t-dsp/t-dsp_desktop_pro/3d_models/so-14-soic14-1.snapshot.2/Renderings/soic-14.JPG

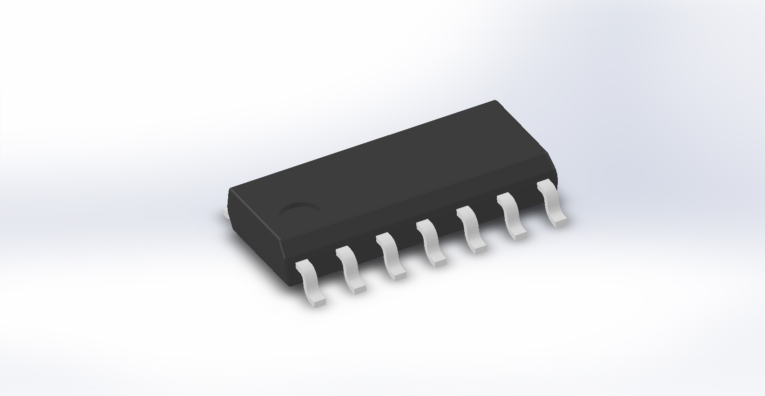
3d_models/so-14-soic14-1.snapshot.2/Renderings/soic-14.JPG
