t-dsp/t-dsp_desktop_pro/3d_models/teensy-4-0-1.snapshot.3/Teensy_4.0/Teensy_4.0_Decal/ARM_Coretex M7 Chip Decal.png

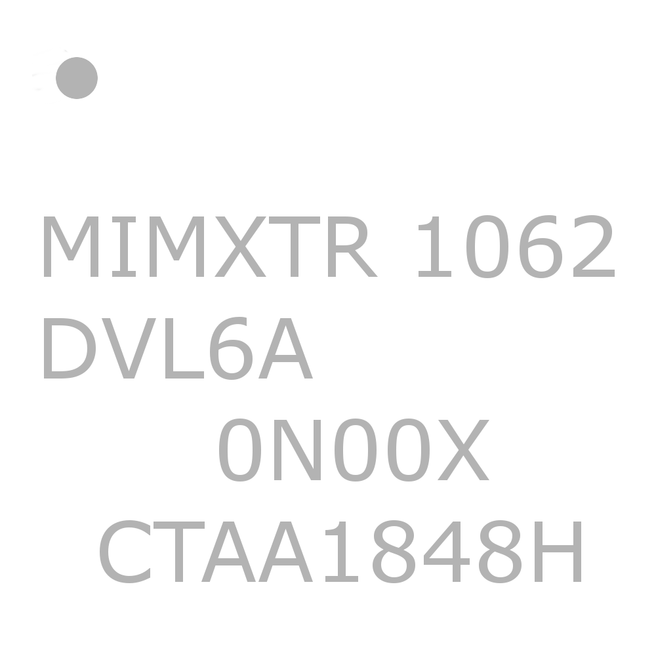
3d_models/teensy-4-0-1.snapshot.3/Teensy_4.0/Teensy_4.0_Decal/ARM_Coretex M7 Chip Decal.png
