t-dsp/t-dsp_desktop_pro/documentation/t-dsp-desktop-pro-3d-angle_back.png

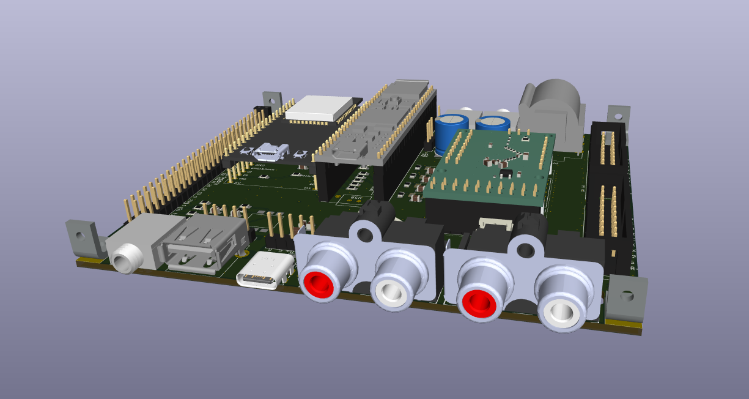
documentation/t-dsp-desktop-pro-3d-angle_back.png
