t-dsp/t-dsp_desktop_pro/documentation/t-dsp-desktop-pro-3d-bottom.png

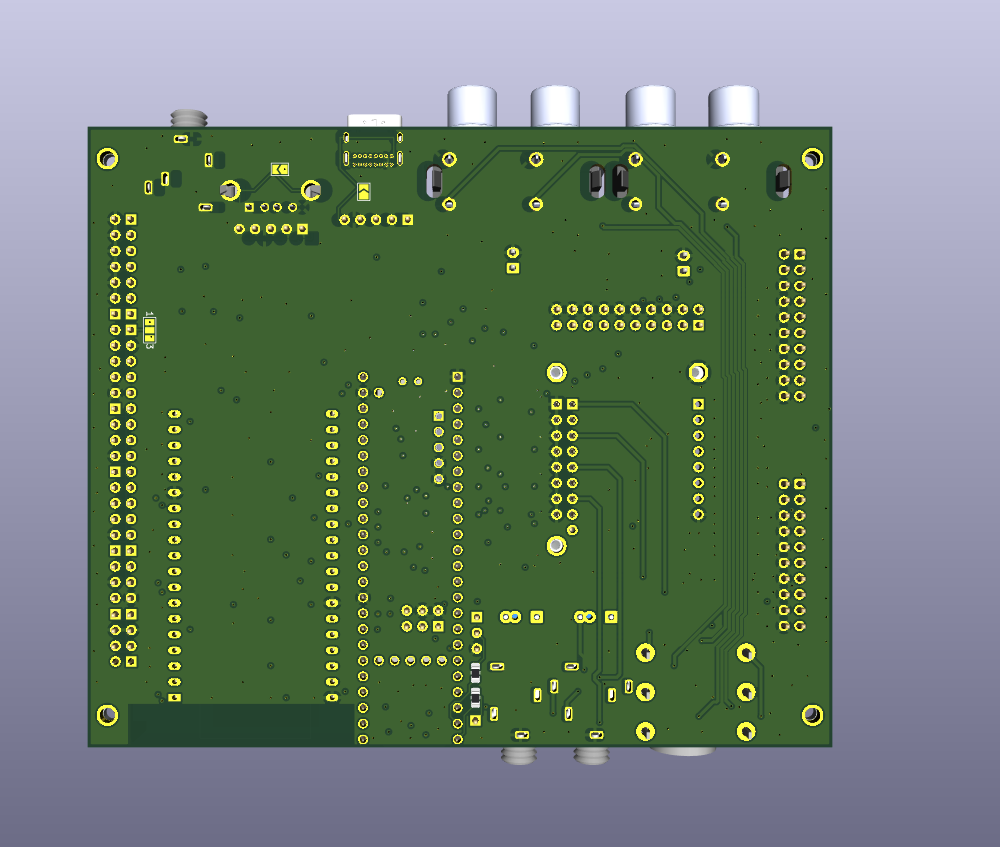
documentation/t-dsp-desktop-pro-3d-bottom.png
