t-dsp/t-dsp_desktop_pro/documentation/t-dsp-desktop-pro-pcb-layout.png

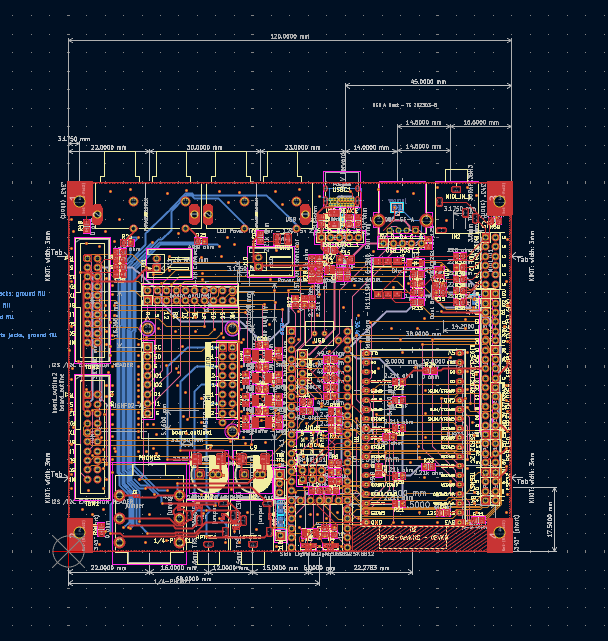
documentation/t-dsp-desktop-pro-pcb-layout.png
