t-dsp/t-dsp_desktop_pro/3d_models/raspberry-pi-4-model-b-1.snapshot.3/Microphone Plug, RPi4ModelB.SLDPRT

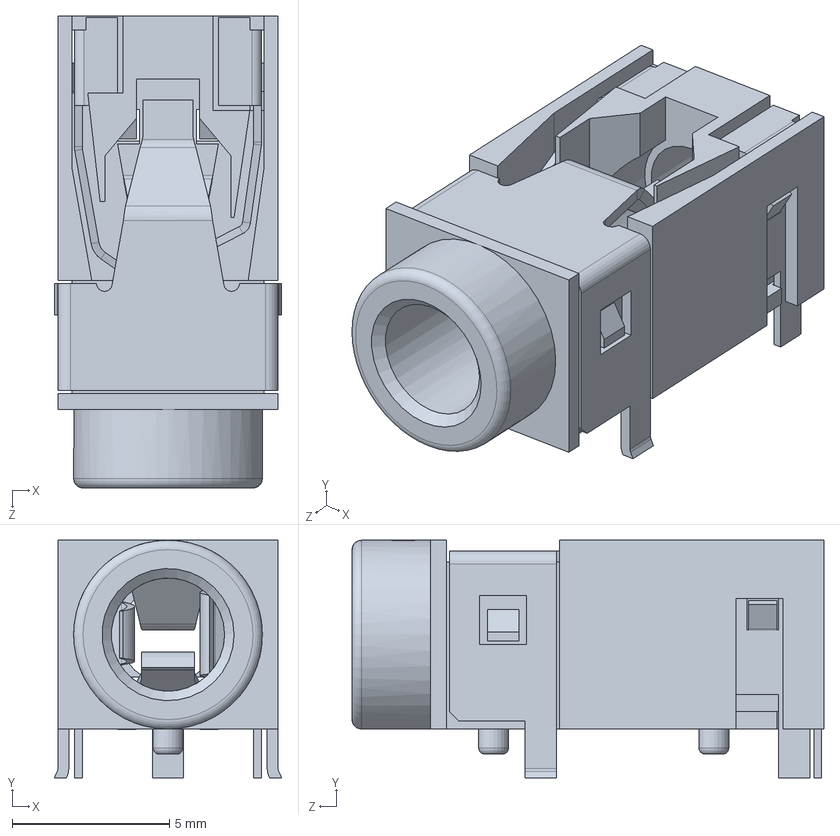
[picture p26: CAD file, 2025-03-24]
3d_models/raspberry-pi-4-model-b-1.snapshot.3/Microphone Plug, RPi4ModelB.SLDPRT
7.23 x 7.55 x 15.0 mm
