t-dsp/t-dsp_desktop_pro/3d_models/raspberry-pi-4-model-b-1.snapshot.3/2.54 mm DUPONT MALE PIN HEADER, POE, 2X2, RPi4ModelB.SLDPRT

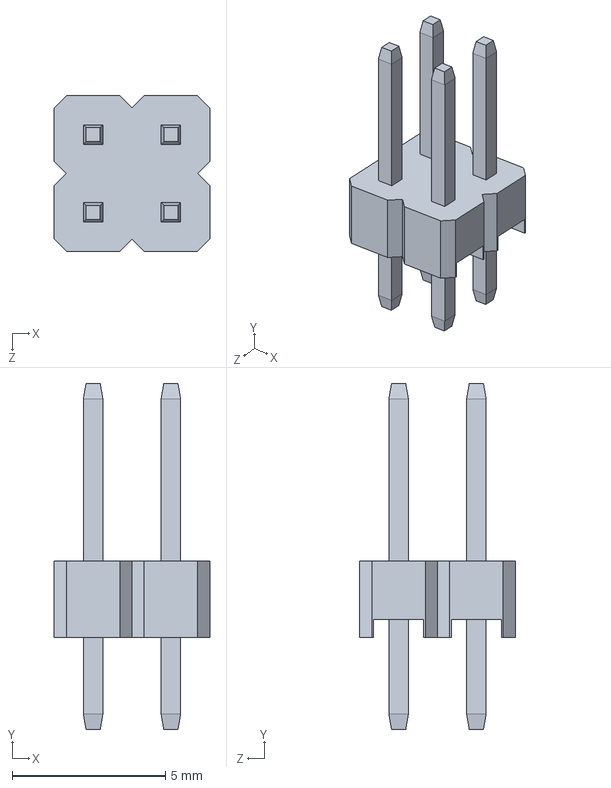
[picture p30: CAD file, 2025-03-24]
3d_models/raspberry-pi-4-model-b-1.snapshot.3/2.54 mm DUPONT MALE PIN HEADER, POE, 2X2, RPi4ModelB.SLDPRT
5.08 x 11.3 x 5.08 mm
