t-dsp/t-dsp_desktop_pro/lib_fp/project_fp/TYPE-C-31-M-12.step

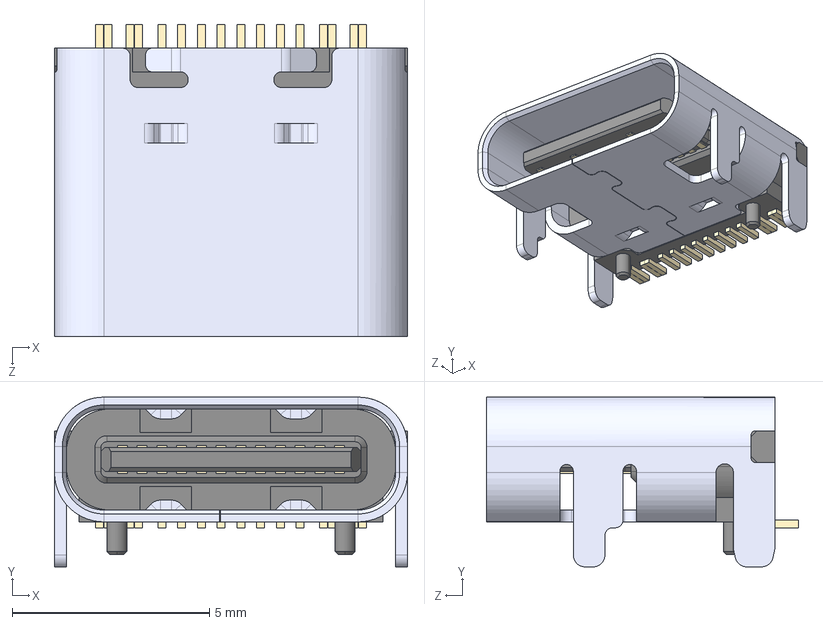
[picture p32: CAD file, 2025-03-24]
lib_fp/project_fp/TYPE-C-31-M-12.step
8.94 x 4.30 x 7.90 mm
