t-dsp/t-dsp_desktop_pro/3d_models/audio_project_board_step/teensy41_audio_project_board_end1.step

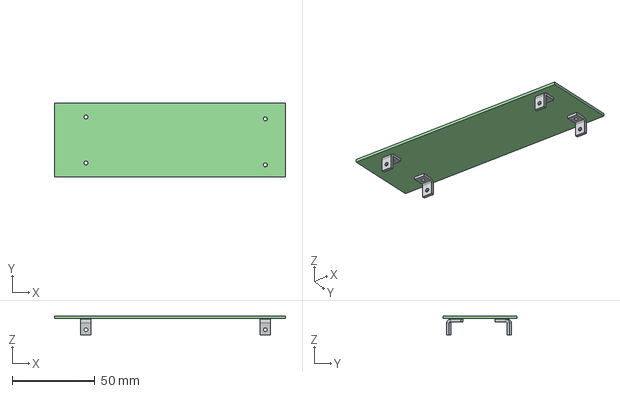
[picture p33: CAD file, 2025-03-24]
3d_models/audio_project_board_step/teensy41_audio_project_board_end1.step
139.7 x 44.5 x 11.5 mm
front_panel PCB
