t-dsp/t-dsp_desktop_pro/3d_models/raspberry-pi-4-model-b-1.snapshot.3/2X USB3.0 PORTS, RPi4ModelB.SLDPRT

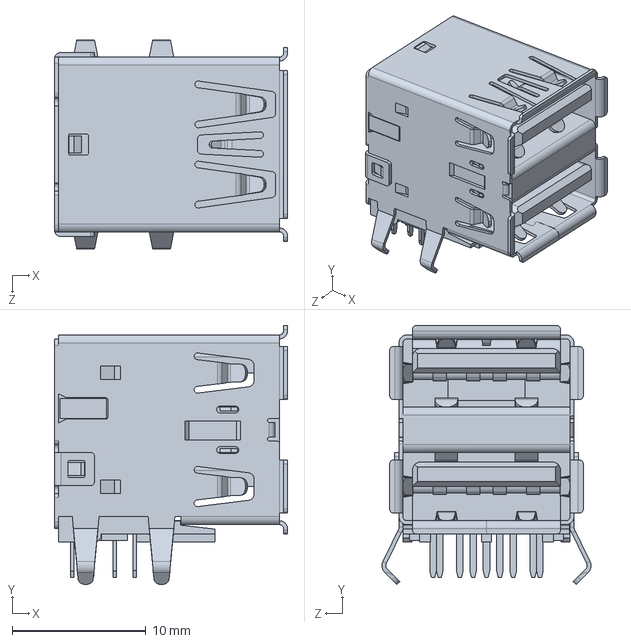
[picture p34: CAD file, 2025-03-24]
3d_models/raspberry-pi-4-model-b-1.snapshot.3/2X USB3.0 PORTS, RPi4ModelB.SLDPRT
17.5 x 19.4 x 15.7 mm
