t-dsp/t-dsp_desktop_pro/3d_models/teensy-4-0-1.snapshot.3/Teensy_4.0/SKRPACE010 v4.SLDPRT

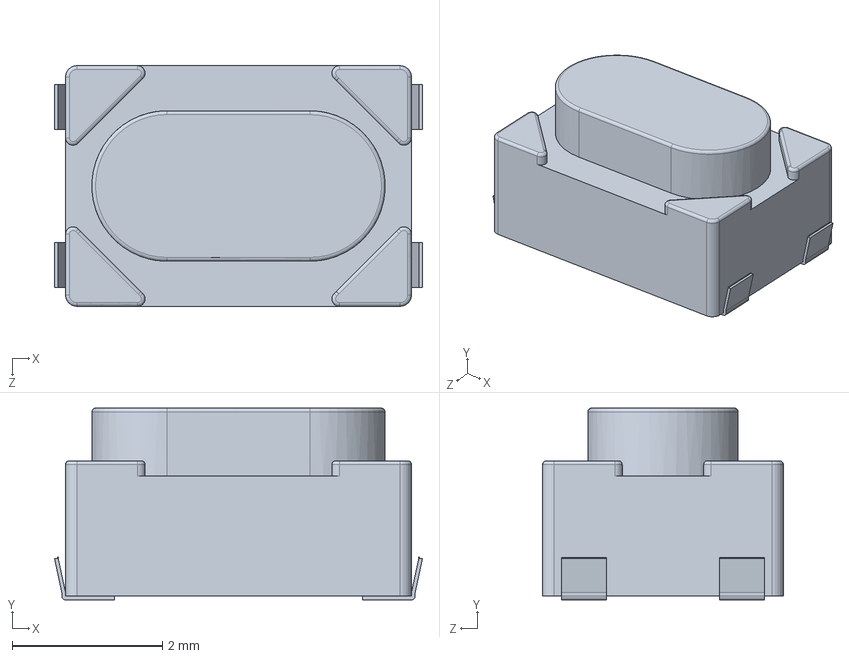
[picture p35: CAD file, 2025-03-24]
3d_models/teensy-4-0-1.snapshot.3/Teensy_4.0/SKRPACE010 v4.SLDPRT
4.89 x 2.55 x 3.20 mm
