t-dsp/t-dsp_desktop_pro/3d_models/TPD4E02B04DQA.step

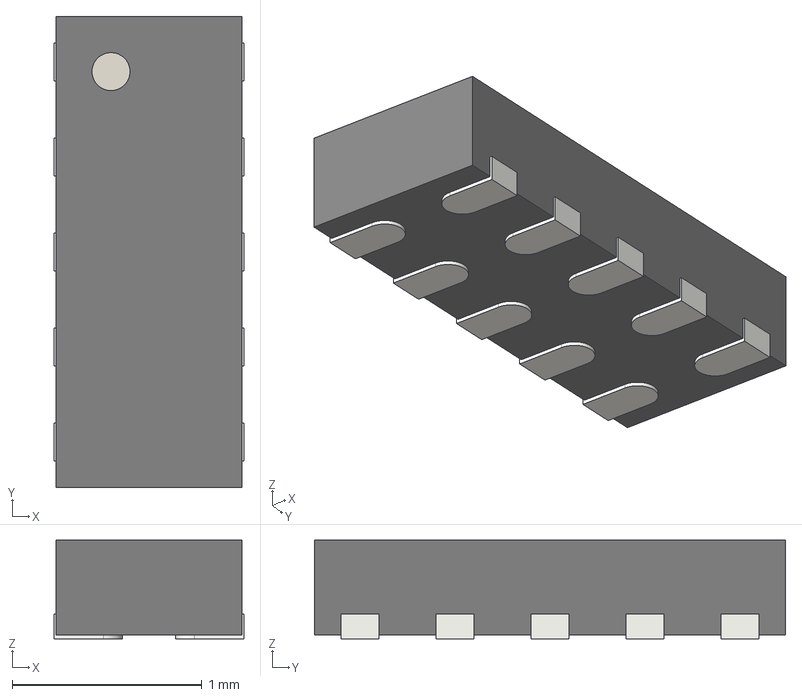
[picture p36: CAD file, 2026-02-23]
3d_models/TPD4E02B04DQA.step
1.00 x 2.48 x 0.52 mm
