t-dsp/t-dsp_desktop_pro/3d_models/audio_project_board_step/teensy41_audio_project_board_fp_c_back.step

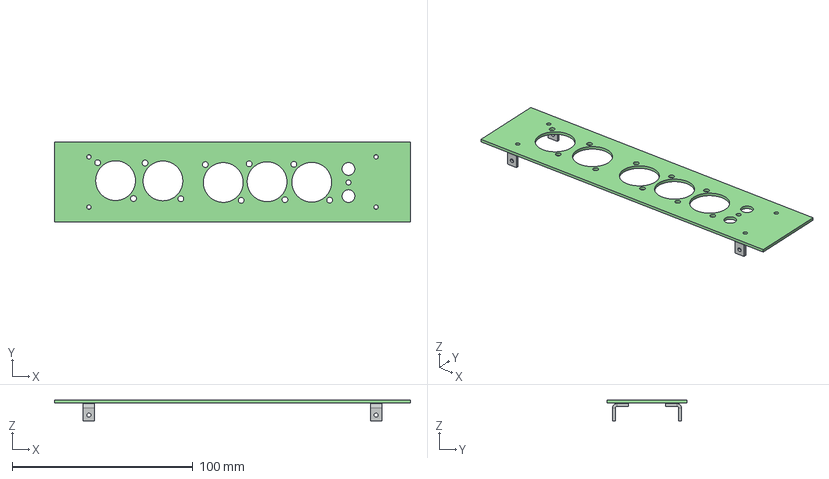
[picture p37: CAD file, 2025-03-24]
3d_models/audio_project_board_step/teensy41_audio_project_board_fp_c_back.step
196.8 x 44.5 x 11.5 mm
front_panel PCB
