t-dsp/t-dsp_desktop_pro/3d_models/raspberry-pi-4-model-b-1.snapshot.3/Broadcom BCM54213PE Gigabit Ethernet Transceiver, RPi4ModelB.SLDPRT

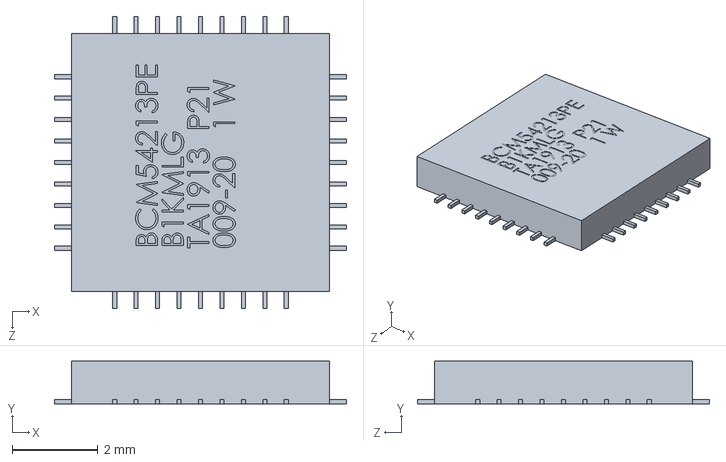
[picture p38: CAD file, 2025-03-24]
3d_models/raspberry-pi-4-model-b-1.snapshot.3/Broadcom BCM54213PE Gigabit Ethernet Transceiver, RPi4ModelB.SLDPRT
6.80 x 1.00 x 6.80 mm
