t-dsp/t-dsp_desktop_pro/3d_models/TPS2116DRLR.stp

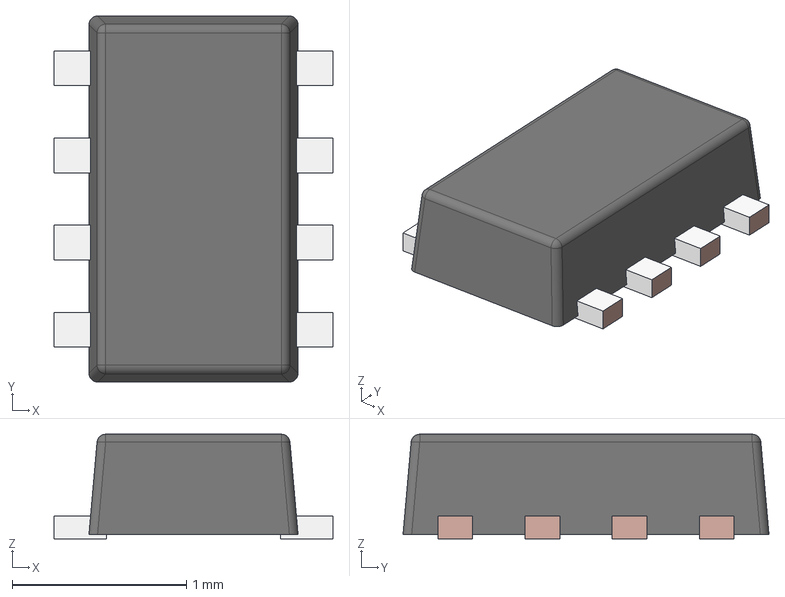
[picture p39: CAD file, 2026-02-23]
3d_models/TPS2116DRLR.stp
1.60 x 2.10 x 0.6 mm
FRAME-DRL0008A
BODY-SOT
