t-dsp/t-dsp_desktop_pro/lib_fp/project_fp/USB4085-GF-A_REVA4.step

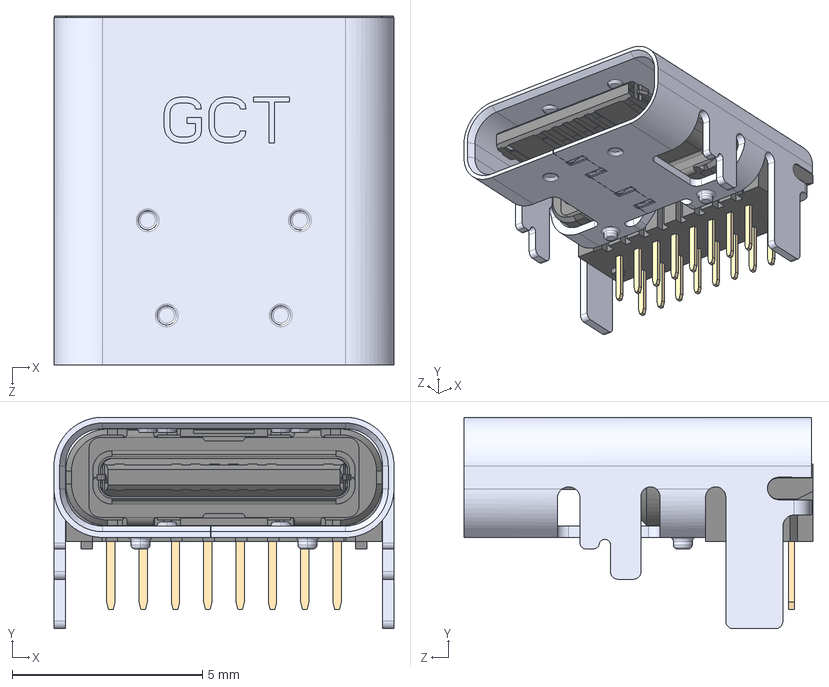
[picture p40: CAD file, 2025-03-24]
lib_fp/project_fp/USB4085-GF-A_REVA4.step
8.94 x 5.56 x 9.17 mm
USB4085-GF-A_PART2
USB4085-GF-A_PART1_1
Part27^USB4085-GF-A_1
