t-dsp/t-dsp_desktop_pro/3d_models/audio_project_board_step/teensy41_audio_project_board_lid.step

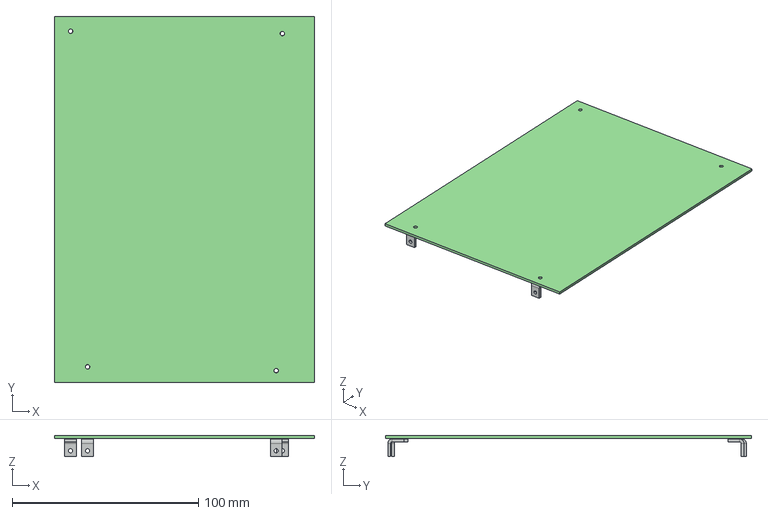
[picture p41: CAD file, 2025-03-24]
3d_models/audio_project_board_step/teensy41_audio_project_board_lid.step
139.7 x 196.8 x 11.5 mm
_autosave-front_panel PCB
