t-dsp/t-dsp_desktop_pro/3d_models/raspberry-pi-4-model-b-1.snapshot.3/VIA VL805 PCIe USB 3.0 controller, RPi4ModelB.SLDPRT

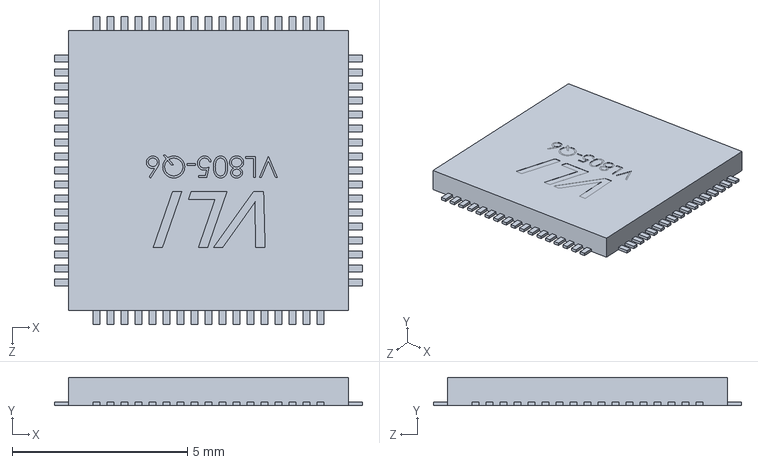
[picture p42: CAD file, 2025-03-24]
3d_models/raspberry-pi-4-model-b-1.snapshot.3/VIA VL805 PCIe USB 3.0 controller, RPi4ModelB.SLDPRT
8.80 x 0.8 x 8.80 mm
