t-dsp/t-dsp_desktop_pro/3d_models/teensy-4-0-1.snapshot.3/Teensy_4.0/Micro USB-B Female 5Pin SMD.SLDPRT

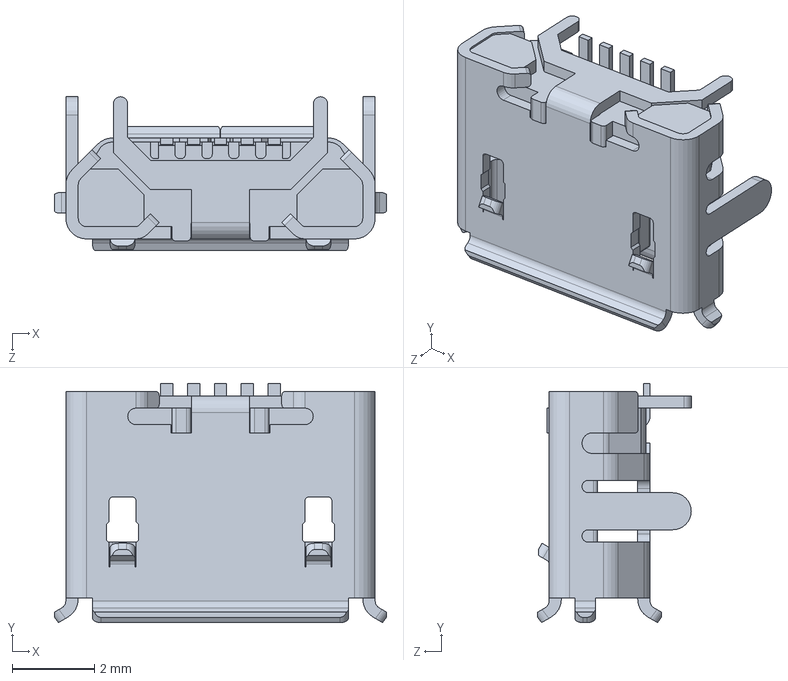
[picture p43: CAD file, 2025-03-24]
3d_models/teensy-4-0-1.snapshot.3/Teensy_4.0/Micro USB-B Female 5Pin SMD.SLDPRT
8.05 x 5.80 x 3.72 mm
