t-dsp/t-dsp_desktop_pro/3d_models/raspberry-pi-4-model-b-1.snapshot.3/2X USB2.0 PORTS, RPi4ModelB.SLDPRT

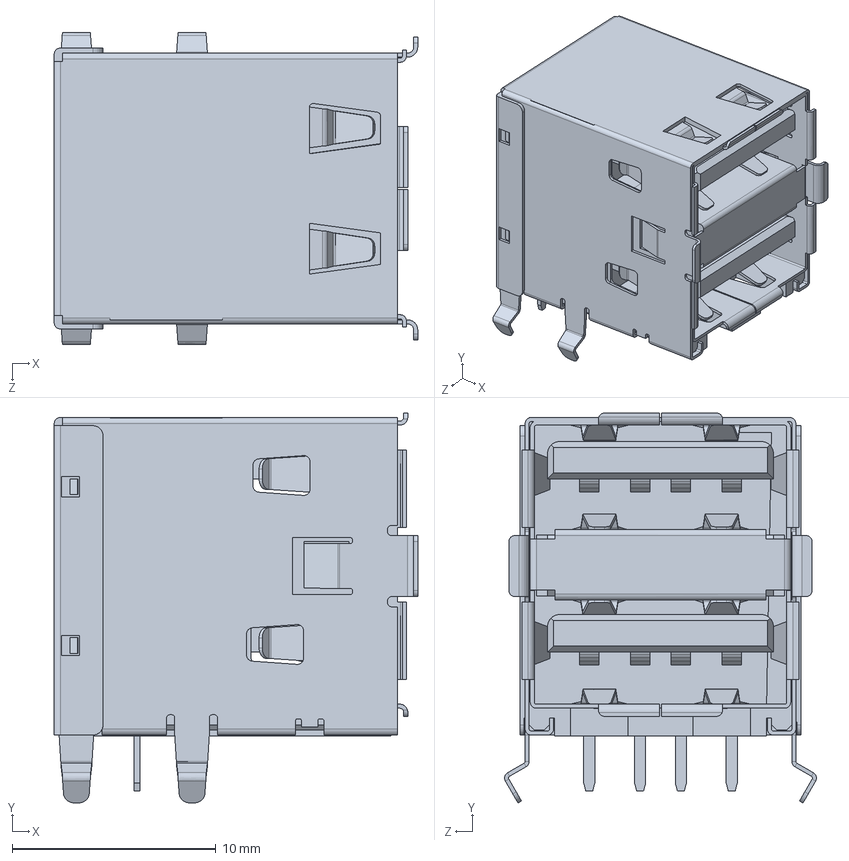
[picture p44: CAD file, 2025-03-24]
3d_models/raspberry-pi-4-model-b-1.snapshot.3/2X USB2.0 PORTS, RPi4ModelB.SLDPRT
17.9 x 19.2 x 15.3 mm
