t-dsp/t-dsp_desktop_pro/3d_models/TPD1E10B06DPYT.stp

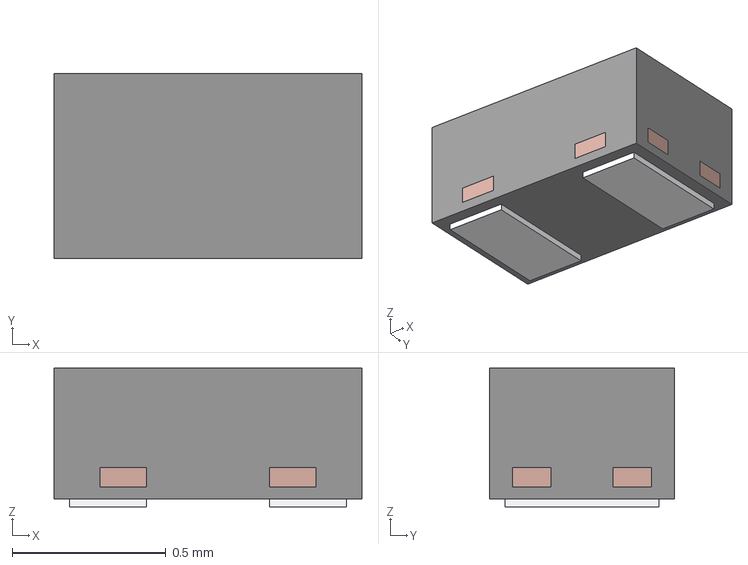
[picture p45: CAD file, 2026-02-23]
3d_models/TPD1E10B06DPYT.stp
1.00 x 0.6 x 0.45 mm
BODY-SON
FRAME-DPY0002A
