t-dsp/t-dsp_desktop_pro/3d_models/JST_EH_S2B-EH_1x02_P2.50mm_Horizontal.step

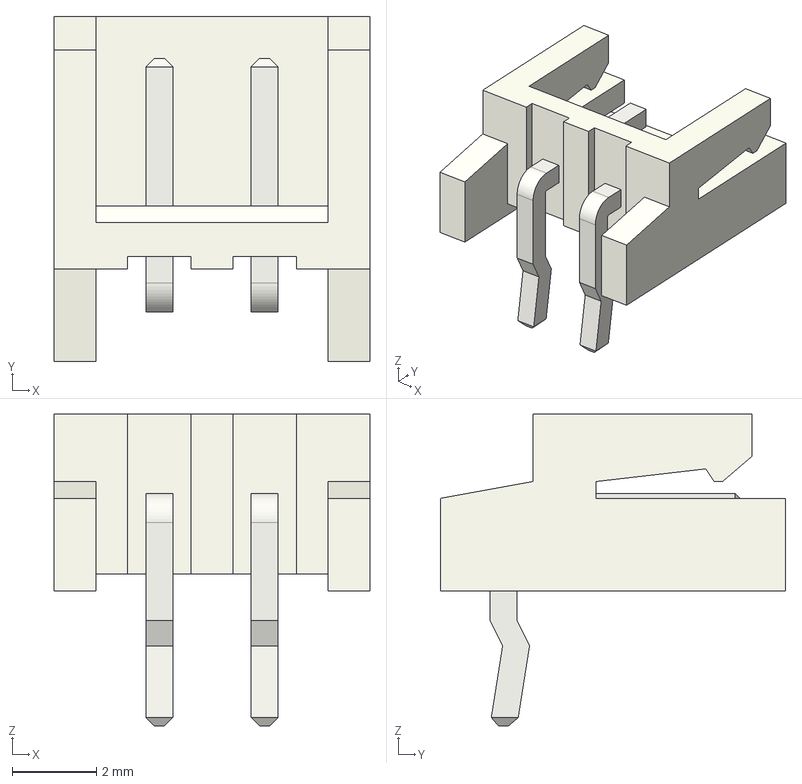
[picture p46: CAD file, 2026-02-20]
3d_models/JST_EH_S2B-EH_1x02_P2.50mm_Horizontal.step
7.50 x 8.20 x 7.40 mm
