t-dsp/t-dsp_desktop_pro/3d_models/raspberry-pi-4-model-b-1.snapshot.3/Female Micro HDMI Connector, RPi4ModelB.SLDPRT

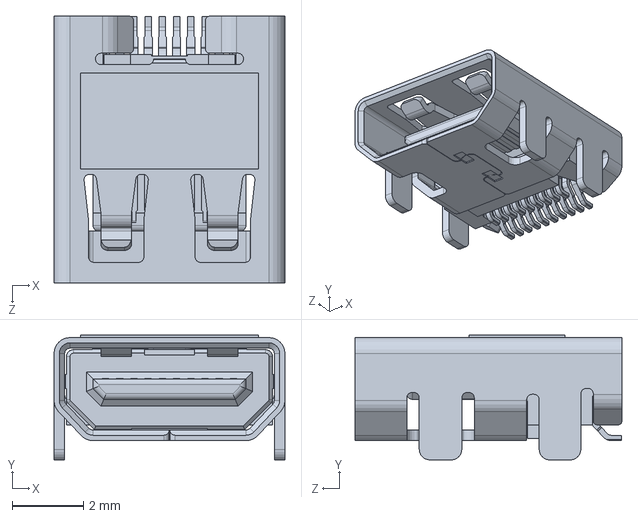
[picture p47: CAD file, 2025-03-24]
3d_models/raspberry-pi-4-model-b-1.snapshot.3/Female Micro HDMI Connector, RPi4ModelB.SLDPRT
6.50 x 3.52 x 7.50 mm
