t-dsp/t-dsp_desktop_pro/3d_models/PinSocket_1x01_P2.54mm_Vertical.step

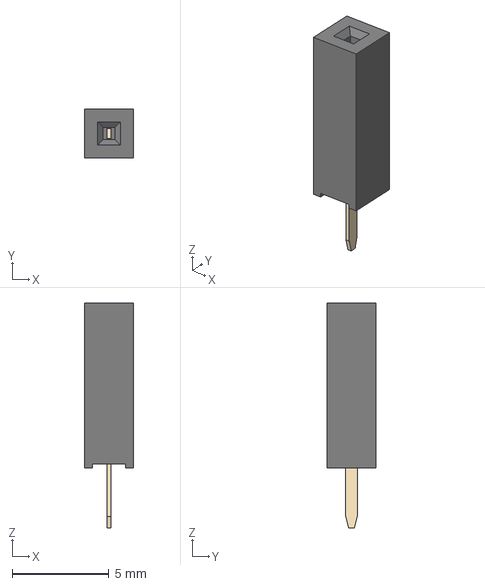
[picture p48: CAD file, 2026-02-20]
3d_models/PinSocket_1x01_P2.54mm_Vertical.step
2.54 x 2.54 x 11.6 mm
