t-dsp/t-dsp_desktop_pro/3d_models/raspberry-pi-4-model-b-1.snapshot.3/Female USB Type C Connector, RPi4ModelB.SLDPRT

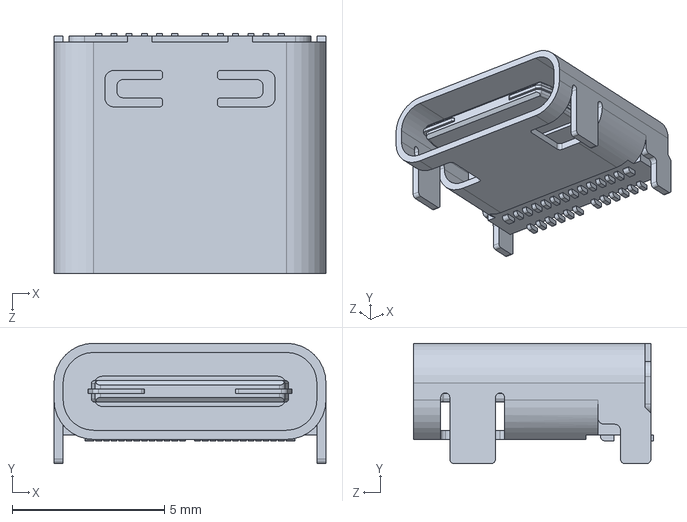
[picture p49: CAD file, 2025-03-24]
3d_models/raspberry-pi-4-model-b-1.snapshot.3/Female USB Type C Connector, RPi4ModelB.SLDPRT
8.94 x 3.96 x 7.90 mm
