t-dsp/t-dsp_desktop_pro/3d_models/H11L1SM.step

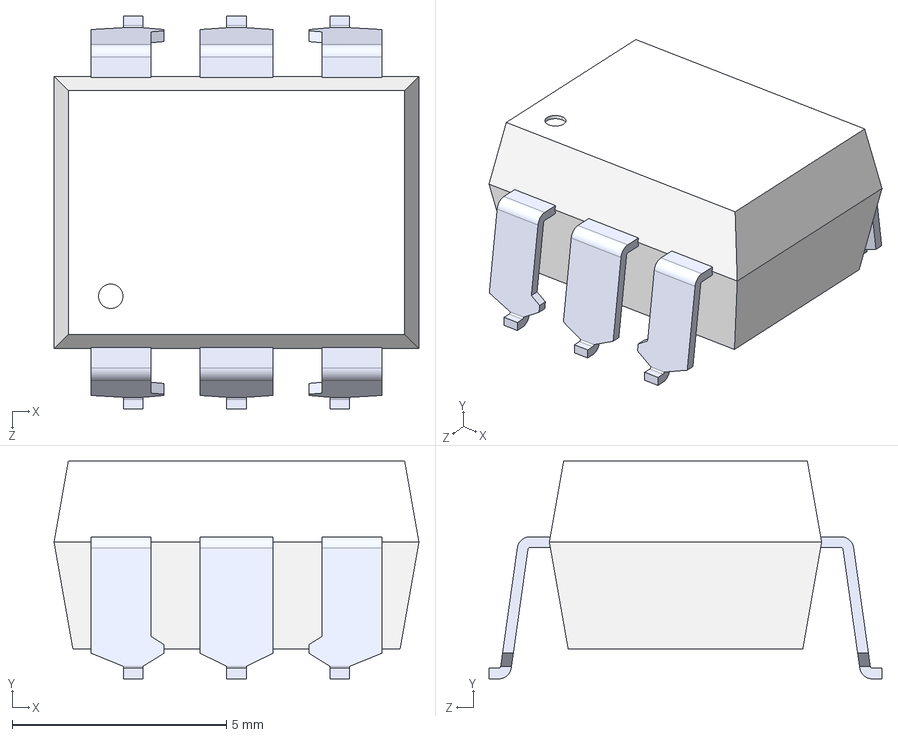
[picture p50: CAD file, 2026-02-20]
3d_models/H11L1SM.step
8.51 x 5.08 x 9.17 mm
