t-dsp/t-dsp_desktop_pro/3d_models/LED_D5.0mm_Clear.step

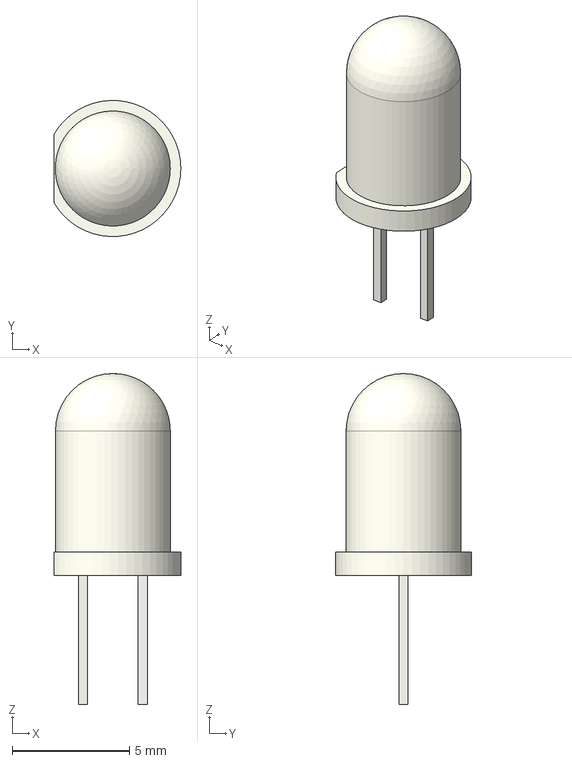
[picture p55: CAD file, 2026-02-20]
3d_models/LED_D5.0mm_Clear.step
5.40 x 5.79 x 14.1 mm
