t-dsp/t-dsp_desktop_pro/3d_models/SOT-23-5.step

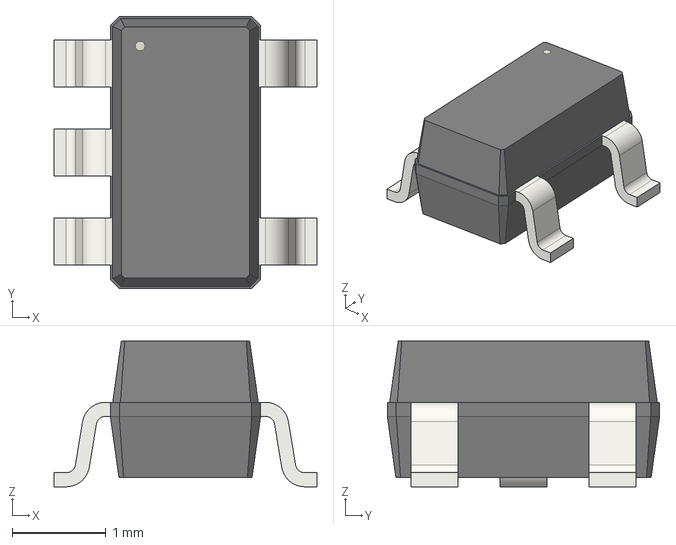
[picture p56: CAD file, 2026-02-20]
3d_models/SOT-23-5.step
2.80 x 2.90 x 1.55 mm
