t-dsp/t-dsp_desktop_pro/3d_models/CP_Radial_D10.0mm_P5.00mm.step

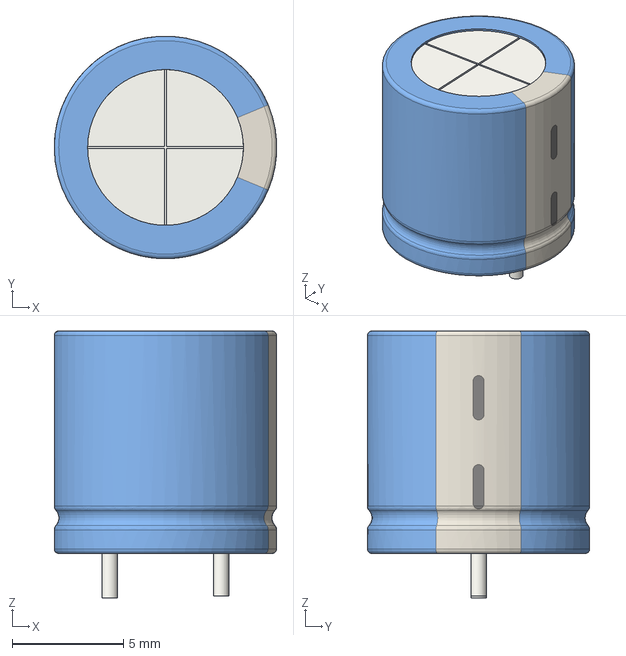
[picture p58: CAD file, 2026-02-11]
3d_models/CP_Radial_D10.0mm_P5.00mm.step
10.00 x 9.99 x 12.0 mm
