t-dsp/t-dsp_desktop_pro/3d_models/D_1210_3225Metric.step

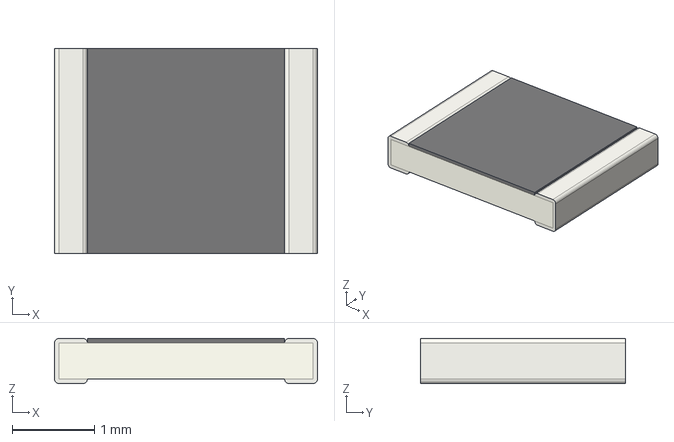
[picture p60: CAD file, 2026-02-11]
3d_models/D_1210_3225Metric.step
3.20 x 2.50 x 0.55 mm
