t-dsp/t-dsp_desktop_pro/3d_models/IDC-Header_2x10_P2.54mm_Vertical.step

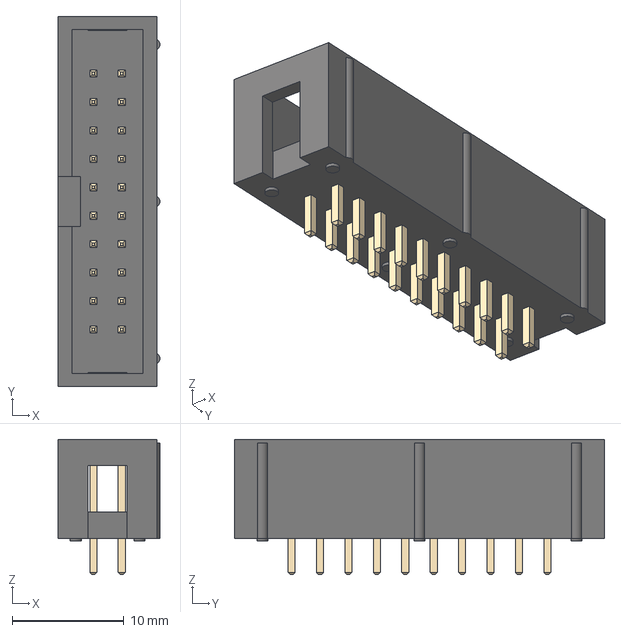
[picture p61: CAD file, 2026-02-11]
3d_models/IDC-Header_2x10_P2.54mm_Vertical.step
9.10 x 33.1 x 12.1 mm
