t-dsp/t-dsp_desktop_pro/3d_models/SOT-583-8.step

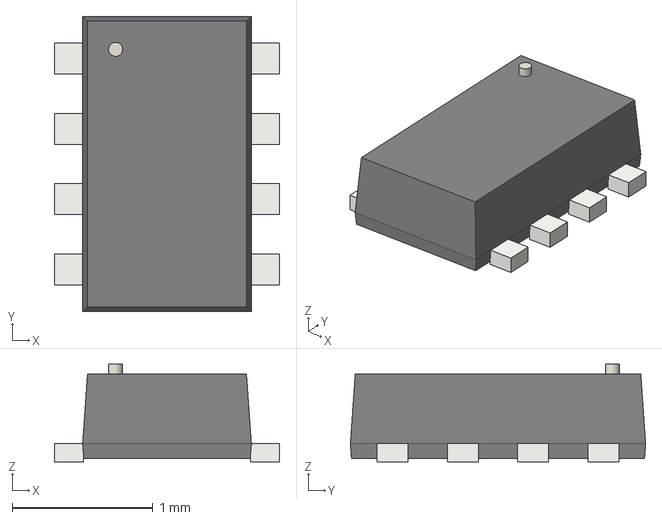
[picture p62: CAD file, 2026-02-11]
3d_models/SOT-583-8.step
1.60 x 2.10 x 0.695 mm
