t-dsp/t-dsp_desktop_pro/3d_models/PinHeader_1x06_P2.54mm_Vertical.step

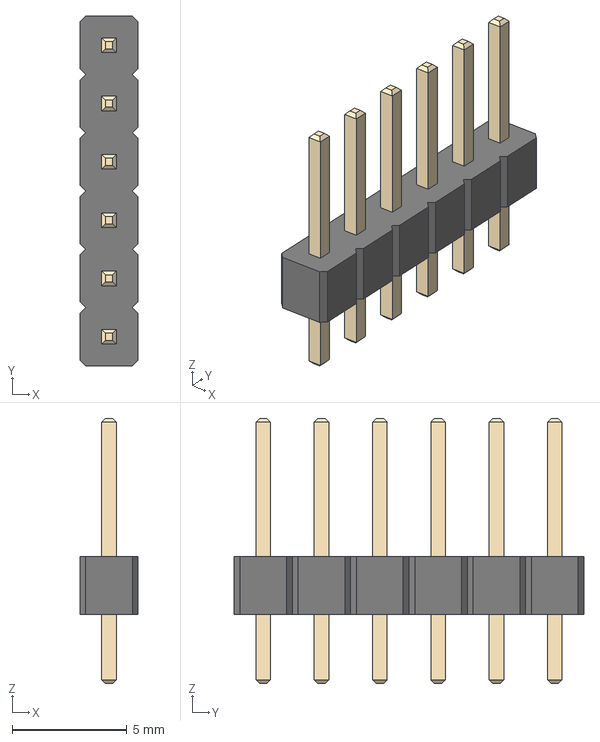
[picture p63: CAD file, 2026-02-11]
3d_models/PinHeader_1x06_P2.54mm_Vertical.step
2.54 x 15.2 x 11.5 mm
