t-dsp/t-dsp_desktop_pro/3d_models/C_1206_3216Metric.step

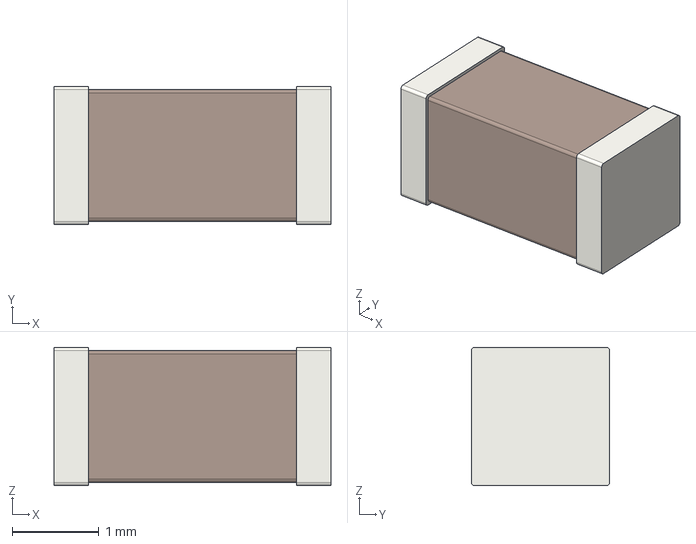
[picture p66: CAD file, 2026-02-11]
3d_models/C_1206_3216Metric.step
3.20 x 1.60 x 1.60 mm
