t-dsp/t-dsp_desktop_pro/3d_models/PinSocket_2x10_P2.54mm_Vertical.step

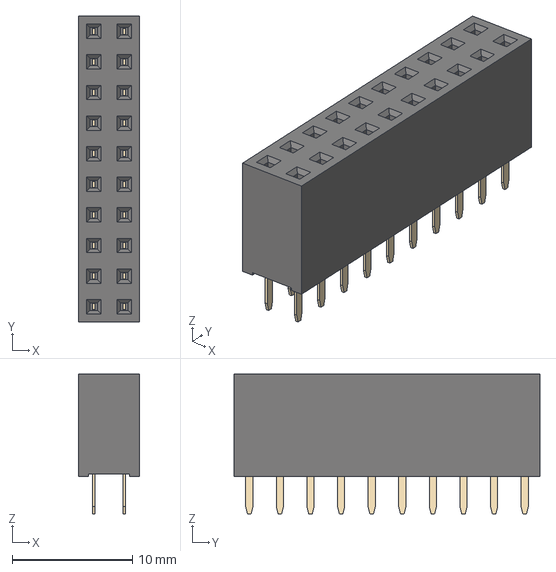
[picture p69: CAD file, 2026-02-11]
3d_models/PinSocket_2x10_P2.54mm_Vertical.step
5.08 x 25.4 x 11.6 mm
