t-dsp/t-dsp_desktop_pro/3d_models/PinSocket_1x02_P2.54mm_Vertical.step

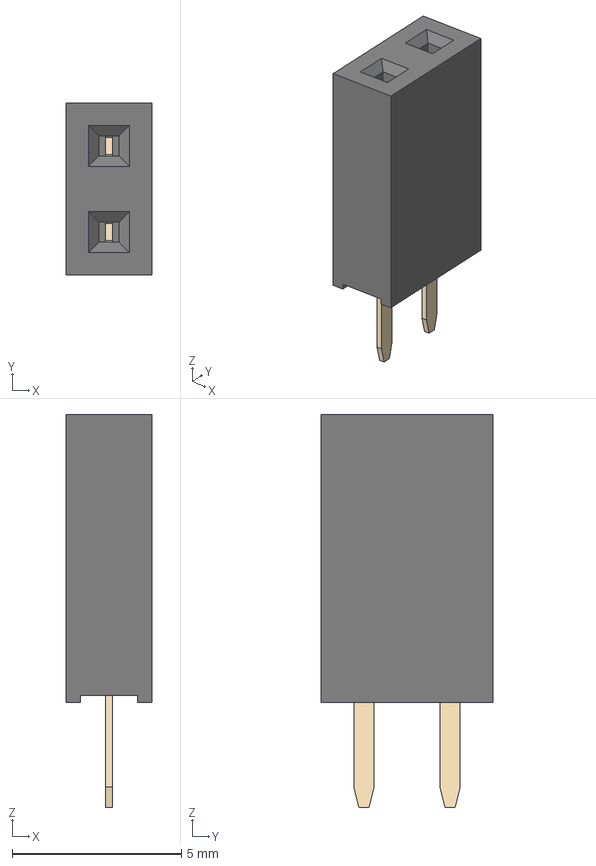
[picture p70: CAD file, 2026-02-11]
3d_models/PinSocket_1x02_P2.54mm_Vertical.step
2.54 x 5.08 x 11.6 mm
