t-dsp/t-dsp_desktop_pro/3d_models/PinHeader_2x03_P2.54mm_Horizontal.step

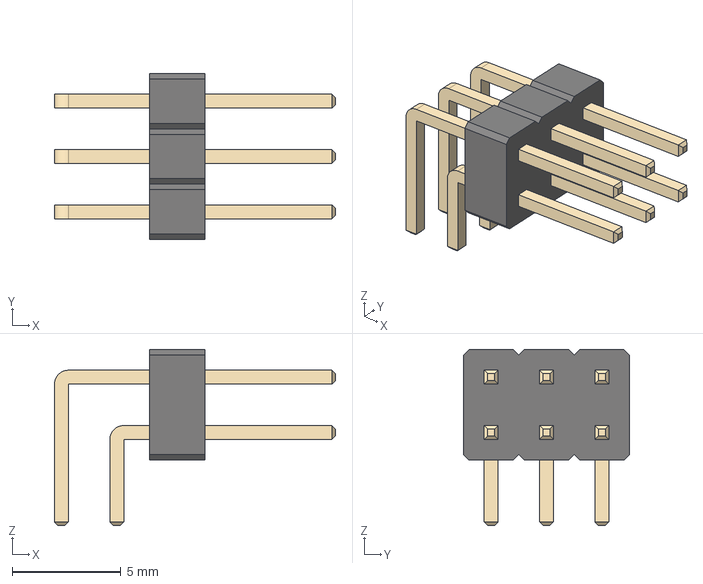
[picture p73: CAD file, 2026-02-11]
3d_models/PinHeader_2x03_P2.54mm_Horizontal.step
12.9 x 7.62 x 8.08 mm
