t-dsp/t-dsp_desktop_pro/3d_models/SN74LVC1G66DBVR.stp

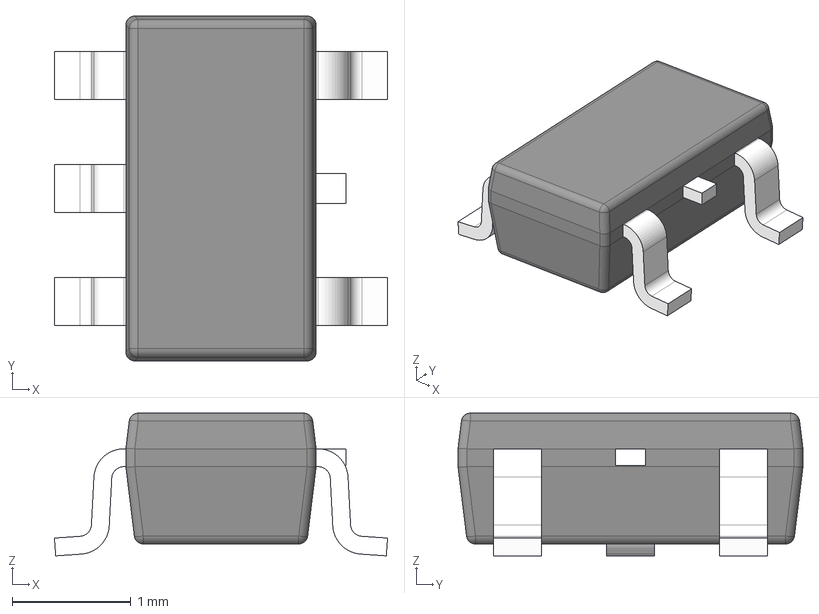
[picture p74: CAD file, 2025-08-25]
3d_models/SN74LVC1G66DBVR.stp
2.80 x 2.90 x 1.20 mm
BODY-SOT
LEAD-SOT x 5
LEAD-DUMMY
