t-dsp/t-dsp_desktop_pro/3d_models/SN74LVC2G125DCTR.step

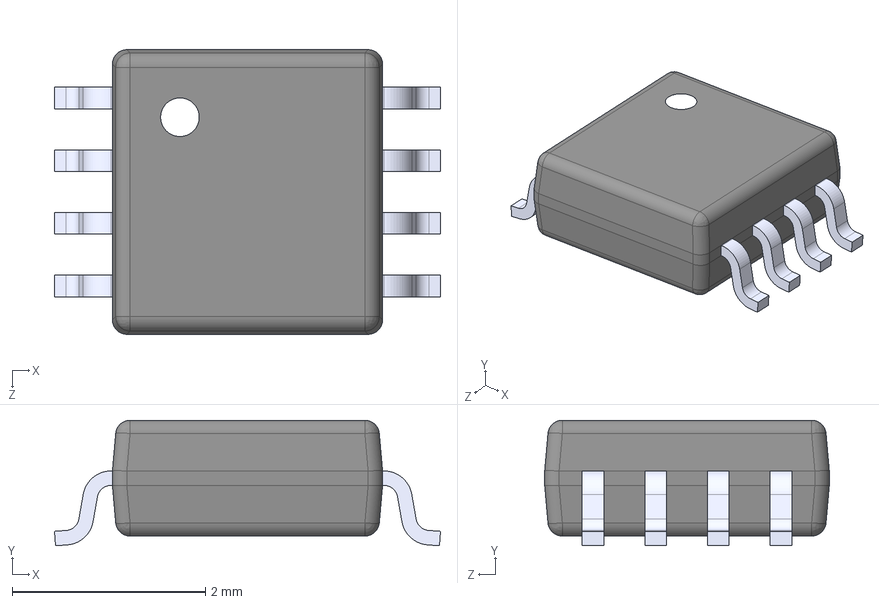
[picture p75: CAD file, 2025-08-24]
3d_models/SN74LVC2G125DCTR.step
4.00 x 1.30 x 2.95 mm
