t-dsp/t-dsp_desktop_pro/3d_models/PJRAS2X1S01X.step

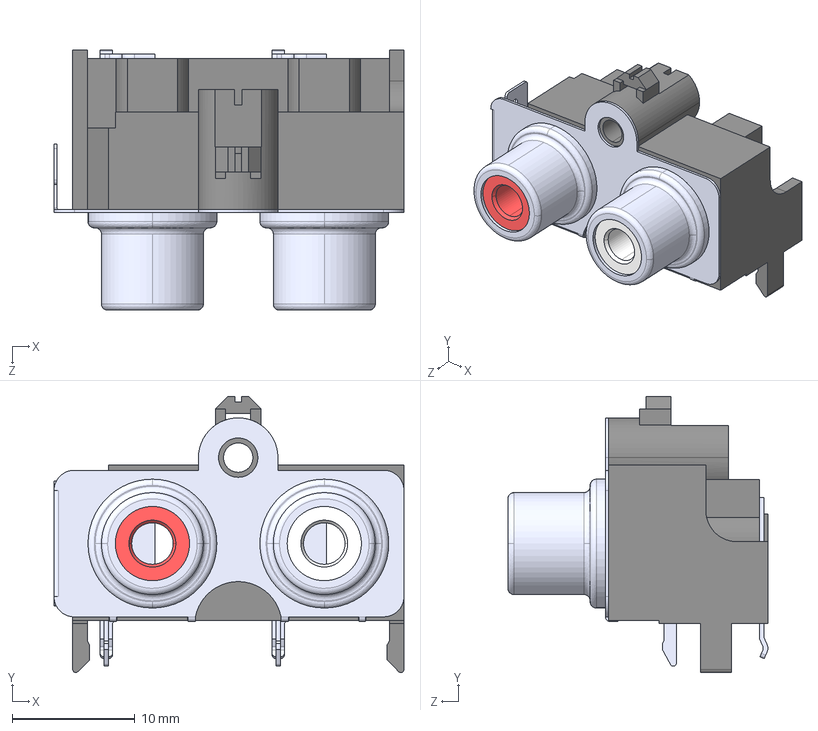
[picture p77: CAD file, 2025-08-21]
3d_models/PJRAS2X1S01X.step
28.5 x 22.5 x 21.2 mm
