t-dsp/t-dsp_desktop_pro/3d_models/EN11-HSM1AF15.STEP

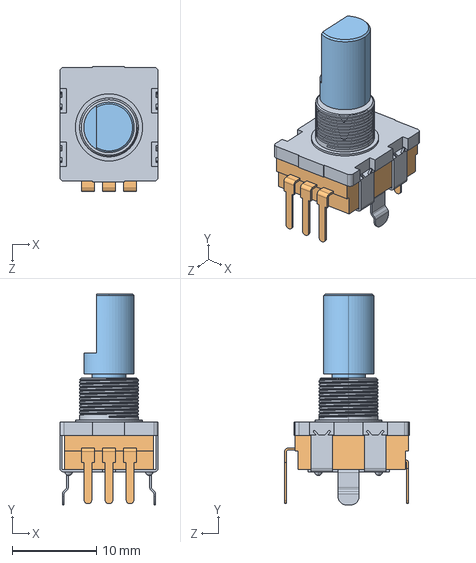
[picture p78: CAD file, 2025-04-17]
3d_models/EN11-HSM1AF15.STEP
11.7 x 25.1 x 14.9 mm
