t-dsp/t-dsp_desktop_pro/3d_models/TFT_320x240_touch_r0.step

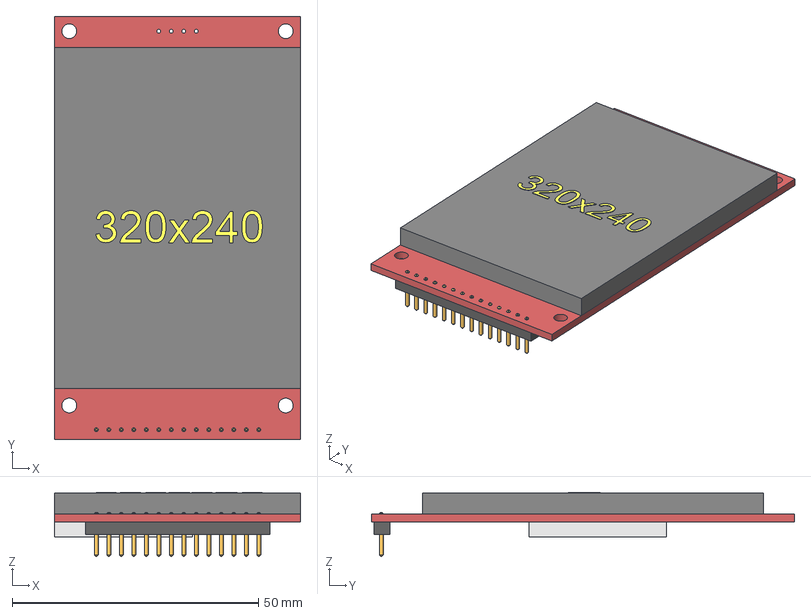
[picture p79: CAD file, 2025-04-06]
3d_models/TFT_320x240_touch_r0.step
50.0 x 86.0 x 13.1 mm
Body-header
Body-pins
Body-display
Body-sdcard
Body-board
