t-dsp/t-dsp_desktop_pro/3d_models/SK6812.step

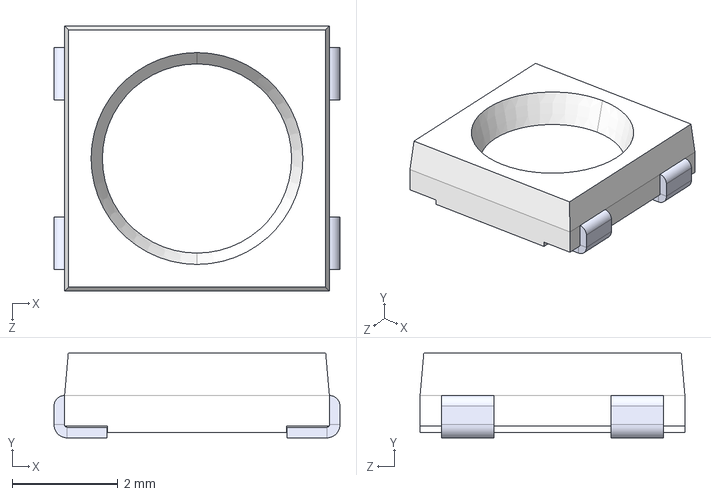
[picture p80: CAD file, 2025-03-26]
3d_models/SK6812.step
5.40 x 1.60 x 5.00 mm
