t-dsp/t-dsp_desktop_pro/3d_models/LED_SK6812MINI-E.step

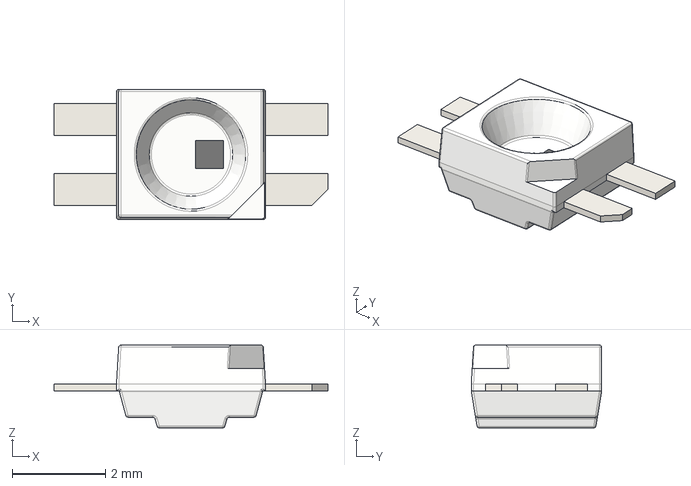
[picture p81: CAD file, 2025-03-26]
3d_models/LED_SK6812MINI-E.step
5.88 x 2.80 x 1.78 mm
