t-dsp/t-dsp_desktop_pro/3d_models/Tactile_Switch_4.54.5MM.stp

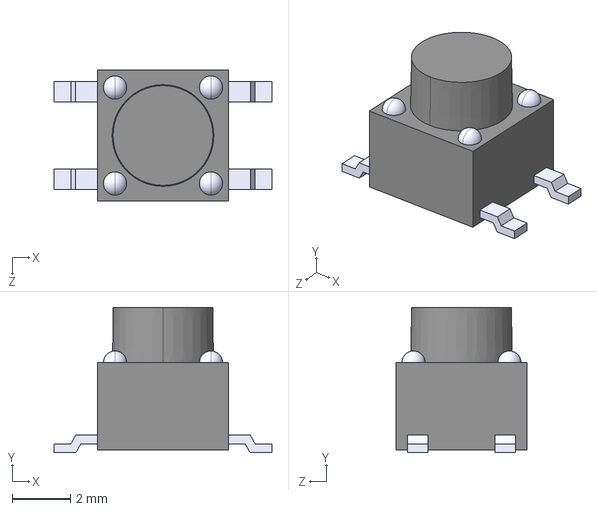
[picture p82: CAD file, 2025-03-26]
3d_models/Tactile_Switch_4.54.5MM.stp
7.50 x 5.00 x 4.50 mm
