t-dsp/t-dsp_desktop_pro/3d_models/c-6364372-2-o-3d.stp

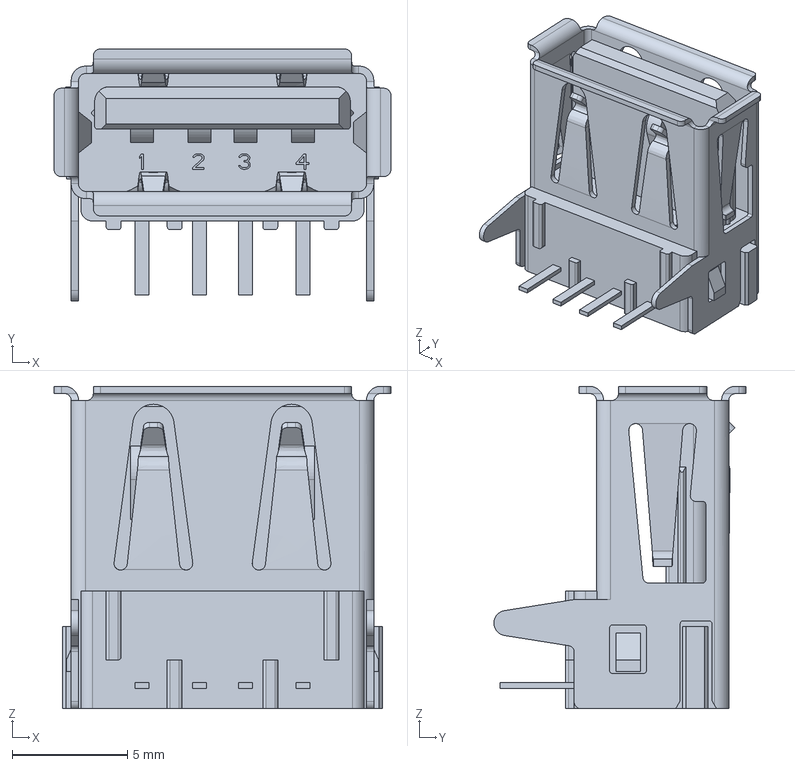
[picture p84: CAD file, 2025-03-24]
3d_models/c-6364372-2-o-3d.stp
14.6 x 10.9 x 14.0 mm
