t-dsp/t-dsp_desktop_pro/3d_models/SJ2-3574A-SMT-TR.step

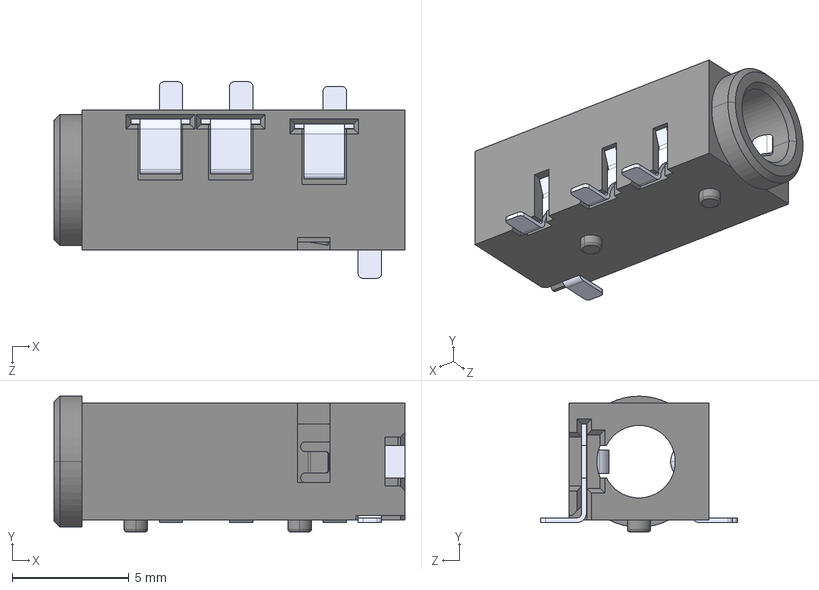
[picture p85: CAD file, 2025-03-24]
3d_models/SJ2-3574A-SMT-TR.step
15.0 x 5.80 x 8.40 mm
