t-dsp/t-dsp_desktop_pro/3d_models/Bracket 4-40 621.STEP

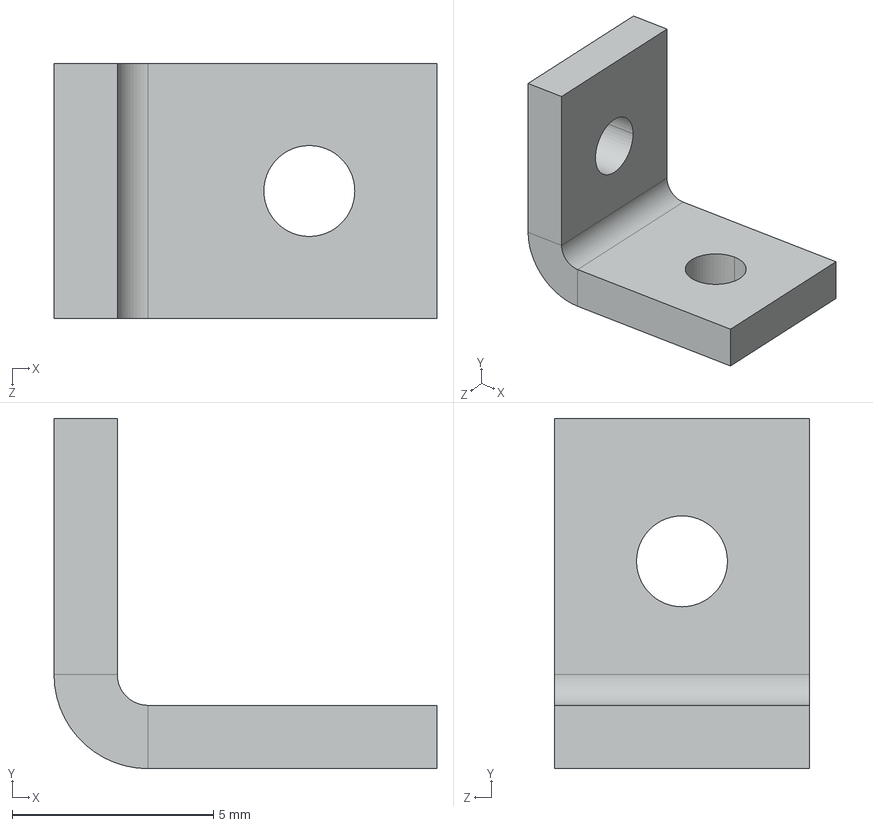
[picture p86: CAD file, 2025-03-24]
3d_models/Bracket 4-40 621.STEP
9.53 x 8.71 x 6.35 mm
