t-dsp/t-dsp_desktop_pro/3d_models/MicroFit3-43045-0428.stp

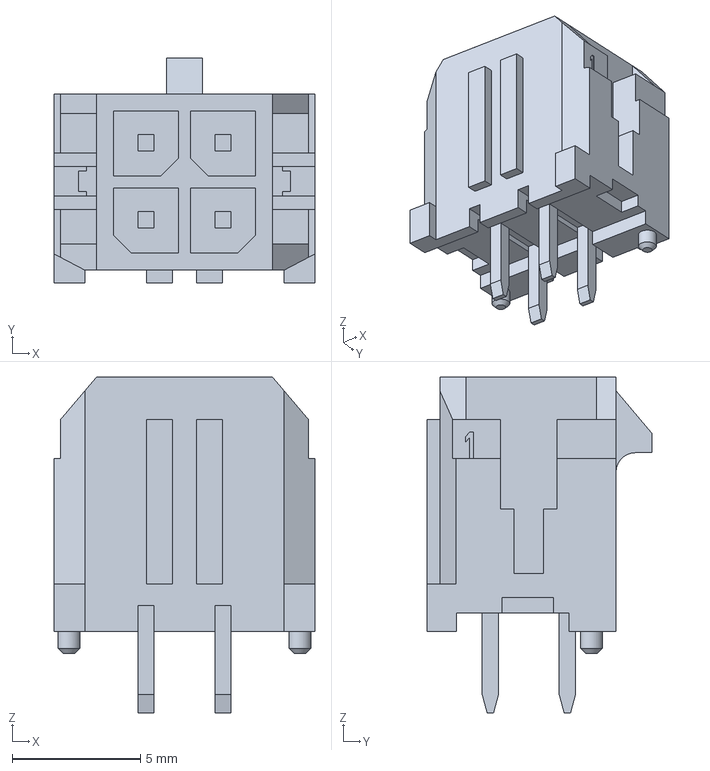
[picture p87: CAD file, 2025-03-24]
3d_models/MicroFit3-43045-0428.stp
10.1 x 8.77 x 13.1 mm
