t-dsp/t-dsp_desktop_pro/3d_models/3-D NC3MAH.stp

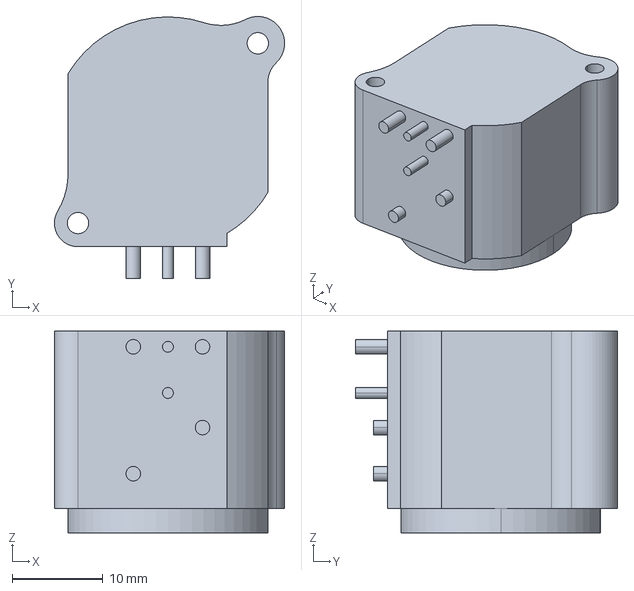
[picture p88: CAD file, 2025-03-24]
3d_models/3-D NC3MAH.stp
25.3 x 28.8 x 22.2 mm
