t-dsp/t-dsp_desktop_pro/3d_models/PinHeader_1x02_P2.54mm_Vertical.step

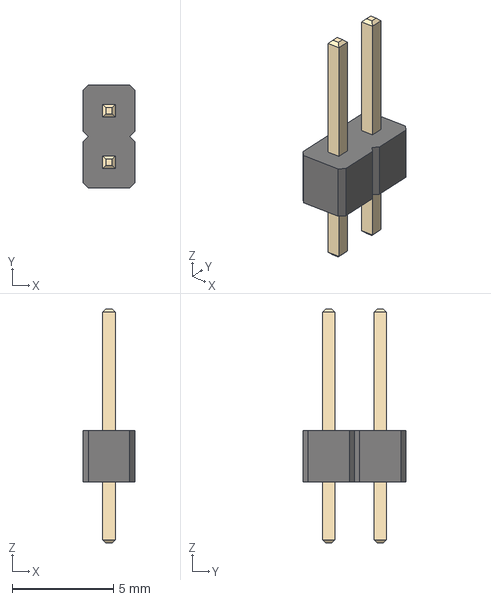
[picture p89: CAD file, 2025-03-24]
3d_models/PinHeader_1x02_P2.54mm_Vertical.step
2.54 x 5.08 x 11.5 mm
