t-dsp/t-dsp_desktop_pro/3d_models/74LS00.step

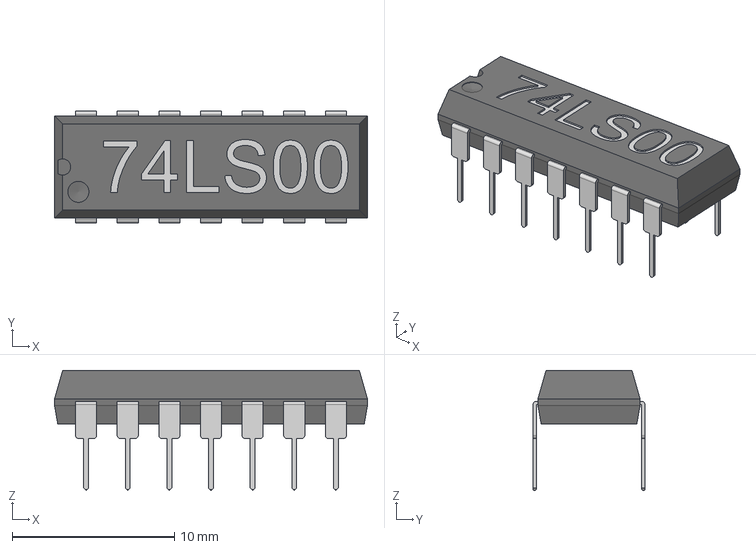
[picture p90: CAD file, 2025-03-24]
3d_models/74LS00.step
19.3 x 6.90 x 7.40 mm
