t-dsp/t-dsp_desktop_pro/3d_models/d-nc3fah.stp

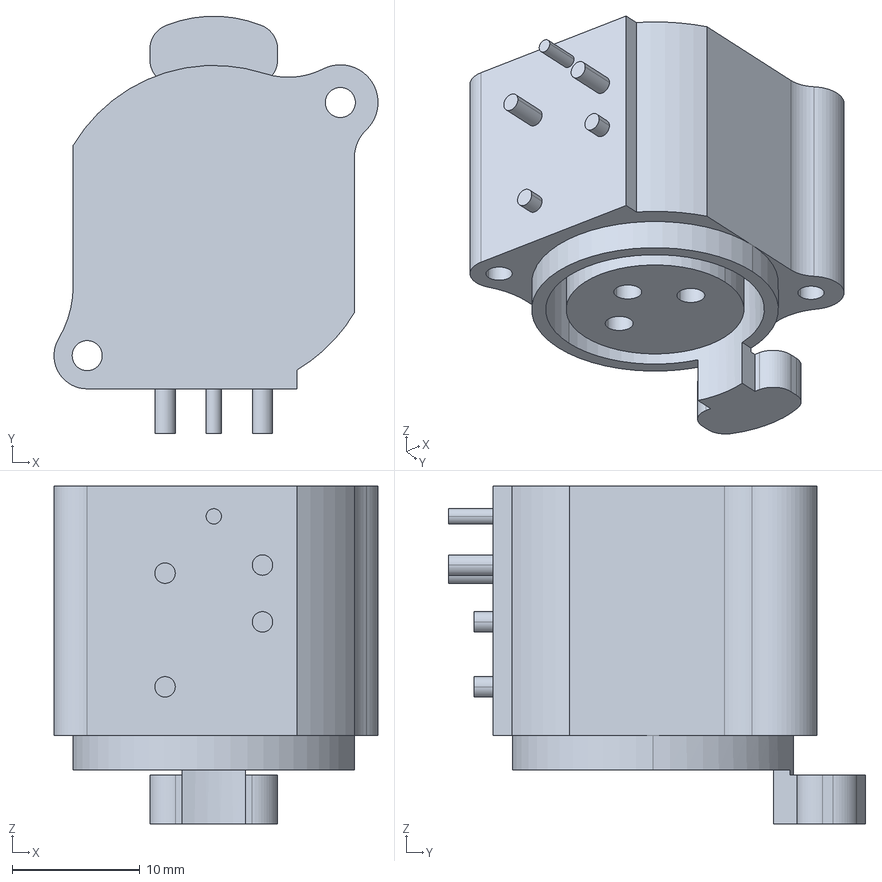
[picture p91: CAD file, 2025-03-24]
3d_models/d-nc3fah.stp
25.3 x 32.6 x 26.4 mm
