t-dsp/t-dsp_desktop_pro/3d_models/COMBO_XLR_NCJ6FI-H-0.stp

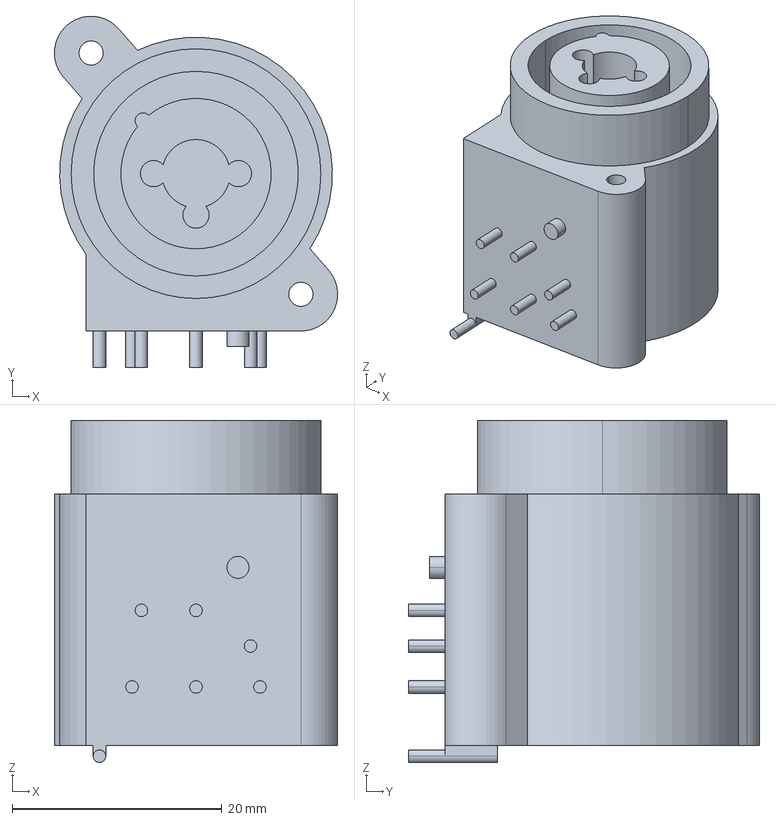
[picture p92: CAD file, 2025-03-24]
3d_models/COMBO_XLR_NCJ6FI-H-0.stp
27.0 x 33.5 x 32.6 mm
