t-dsp/t-dsp_desktop_pro/3d_models/COMBO-NCJ6FA-H.step

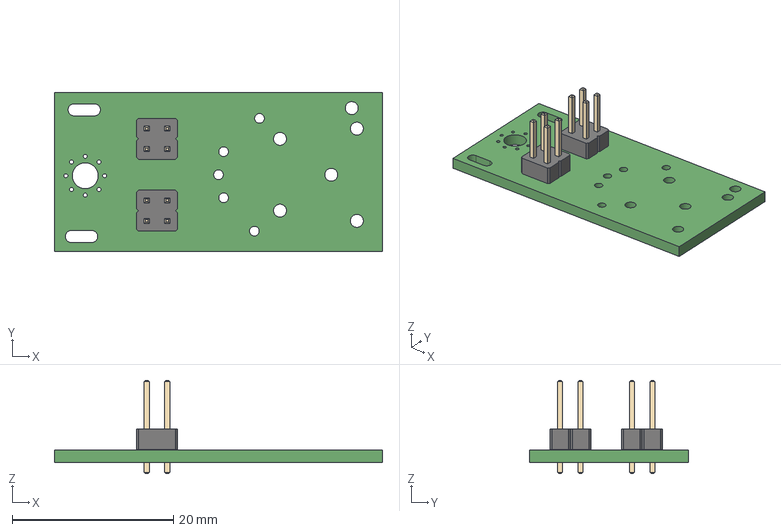
[picture p93: CAD file, 2025-03-24]
3d_models/COMBO-NCJ6FA-H.step
40.6 x 19.7 x 11.5 mm
