t-dsp/t-dsp_desktop_pro/3d_models/35RAPC7JS_SIMPLIFIED.step

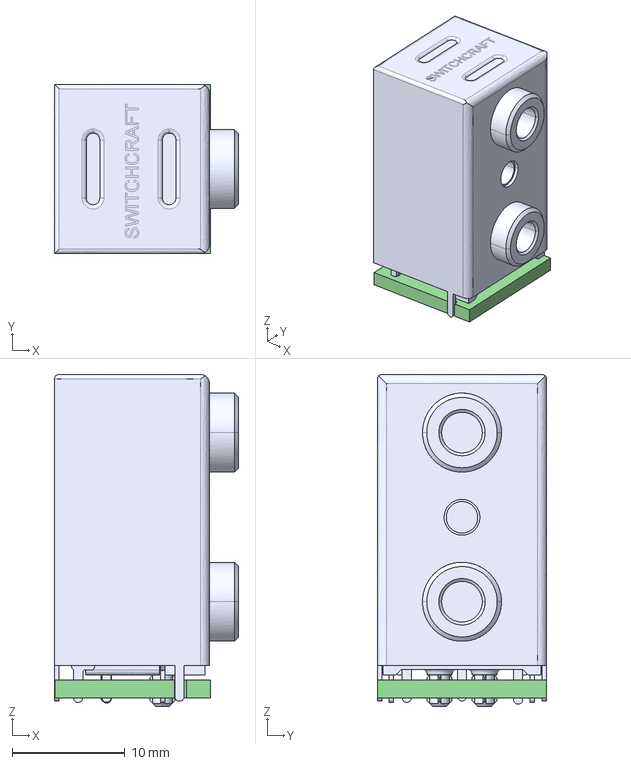
[picture p94: CAD file, 2025-03-24]
3d_models/35RAPC7JS_SIMPLIFIED.step
16.4 x 15.0 x 29.5 mm
IO_3.5_35RAPC7JS PCB
