t-dsp/t-dsp_desktop_pro/3d_models/SD_CARD_DM3D-SF.step

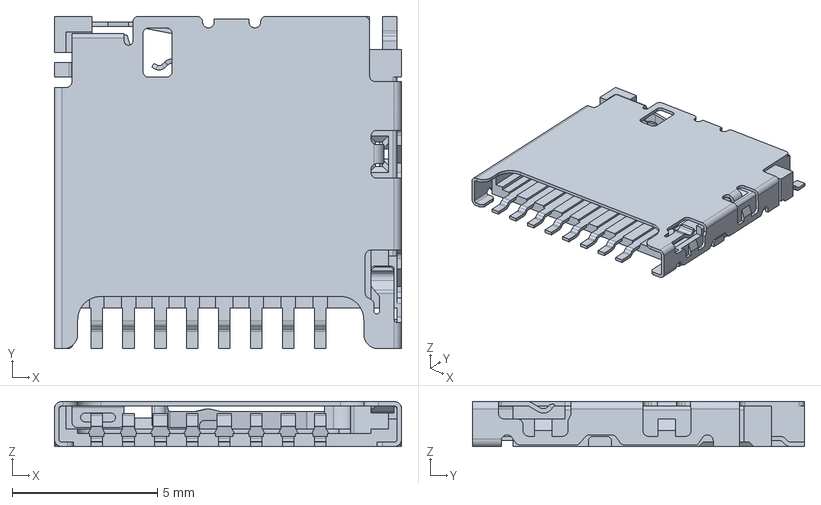
[picture p95: CAD file, 2025-03-24]
3d_models/SD_CARD_DM3D-SF.step
11.9 x 11.4 x 1.55 mm
