t-dsp/t-dsp_desktop_pro/3d_models/ncj6fah-3.dxf

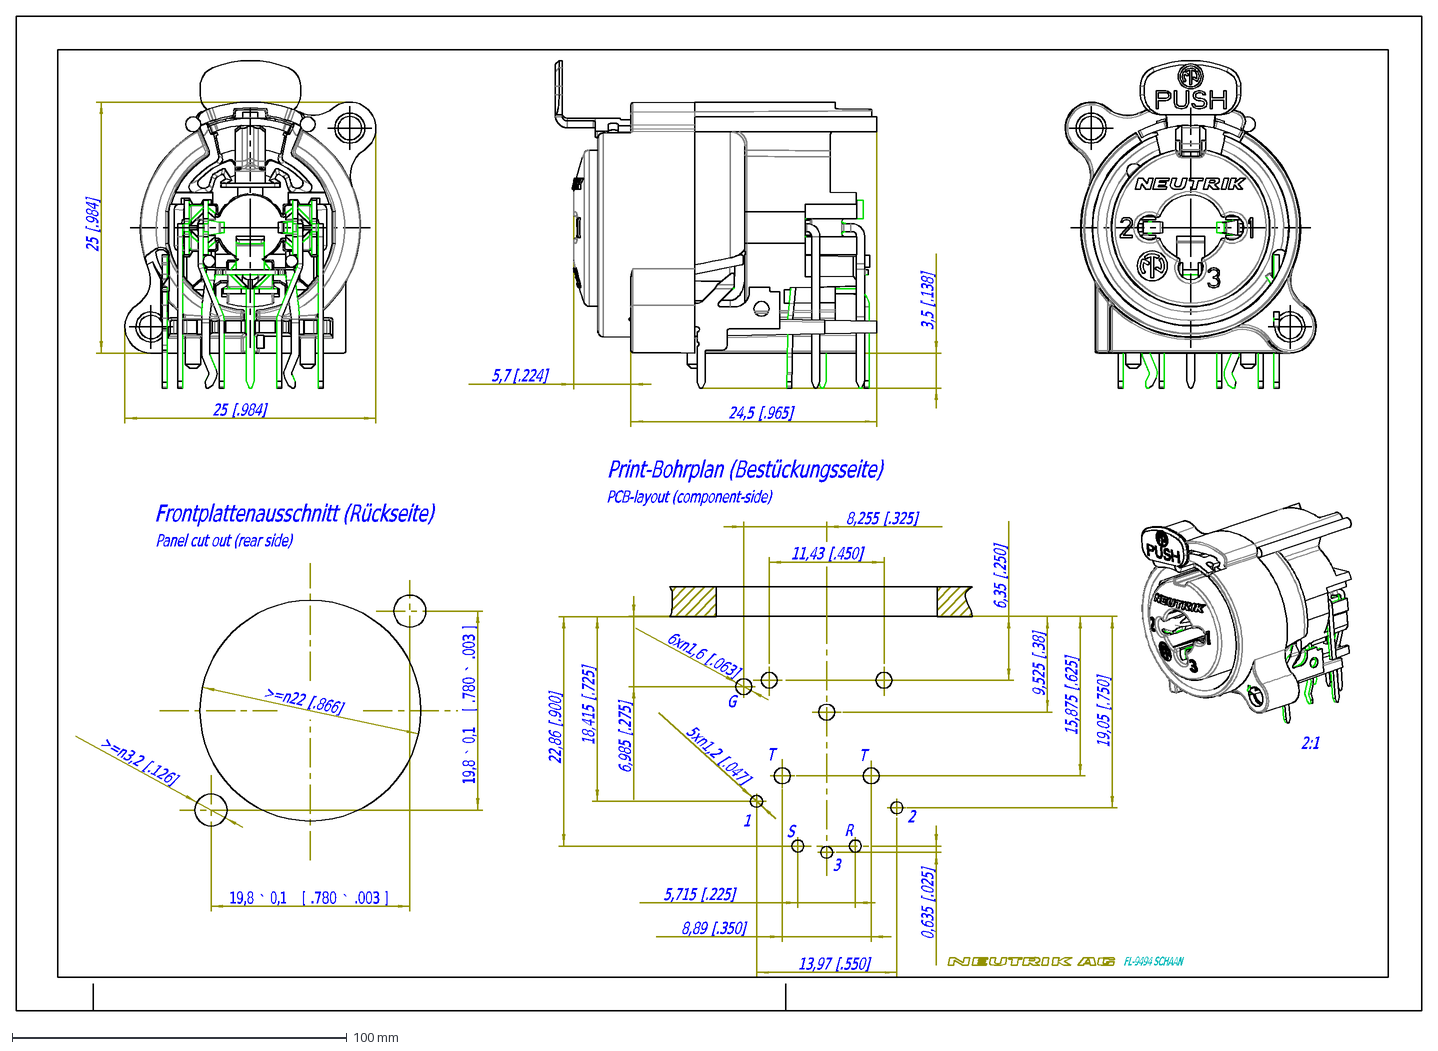
[picture p96: CAD file, 2025-03-24]
3d_models/ncj6fah-3.dxf
FL-9494 SCHAAN
19,8
0,1
[
.780
.003
]
8,89 [.350]
8,255 [.325]
13,97 [.550]
5,715 [.225]
6,985 [.275]
22,86 [.900]
15,875 [.625]
19,05 [.750]
0,635 [.025]
6,35 [.250]
11,43 [.450]
18,415 [.725]
25 [.984]
5,7 [.224]
3,5 [.138]
24,5 [.965]
9,525 [.38]
Print-Bohrplan (Bestückungsseite)
PCB-layout (component-side)
G
1
2
3
T
S
R
Frontplattenausschnitt (Rückseite)
Panel cut out (rear side)
2:1
