t-dsp/t-dsp_desktop_pro/3d_models/c-292304-1-b-3d.stp

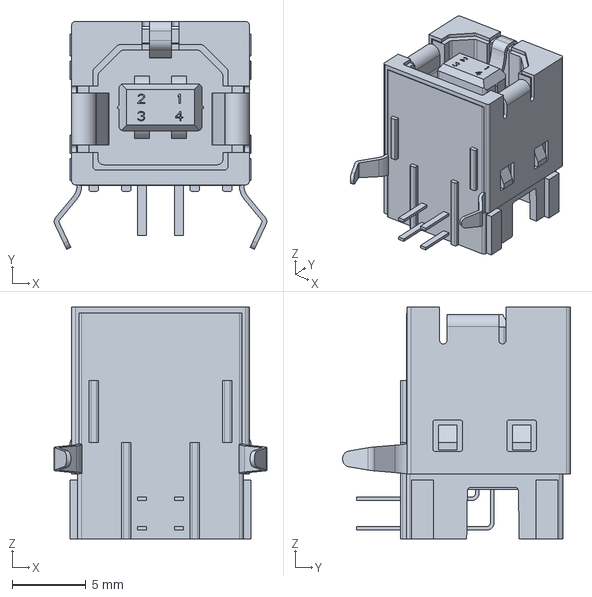
[picture p97: CAD file, 2025-03-24]
3d_models/c-292304-1-b-3d.stp
14.4 x 15.4 x 15.7 mm
