t-dsp/t-dsp_desktop_pro/3d_models/T10W--3DModel-STEP-56544.STEP

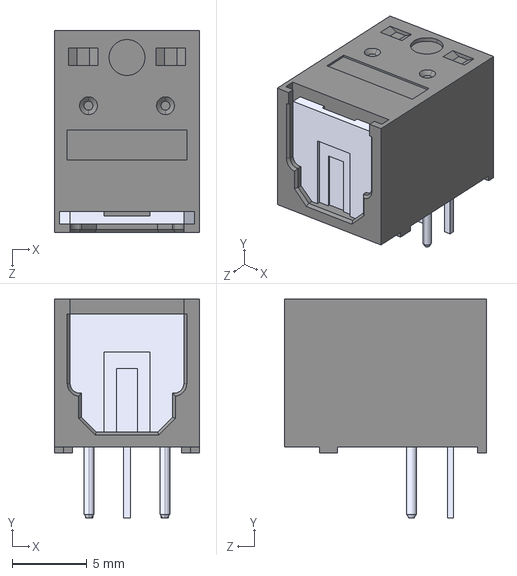
[picture p98: CAD file, 2025-03-24]
3d_models/T10W--3DModel-STEP-56544.STEP
9.70 x 14.7 x 13.5 mm
