t-dsp/t-dsp_desktop_pro/3d_models/DIN-5.STEP

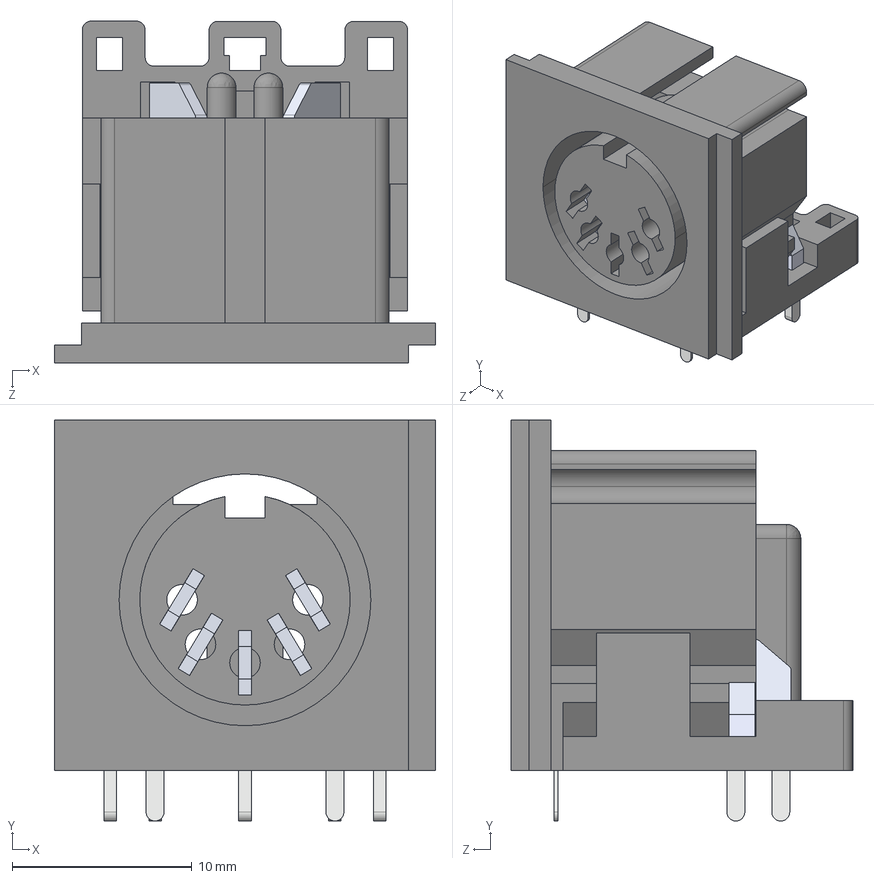
[picture p99: CAD file, 2025-03-24]
3d_models/DIN-5.STEP
21.2 x 22.3 x 19.0 mm
DIN5 A
DIN5 B
DIN5 C
DIN D x 2
DIN E x 2
DIN EE x 2
DIN G
DIN DD x 2
