t-dsp/t-dsp_desktop_pro/3d_models/TOSLINK_3D_MODEL_PLT133_T9.step

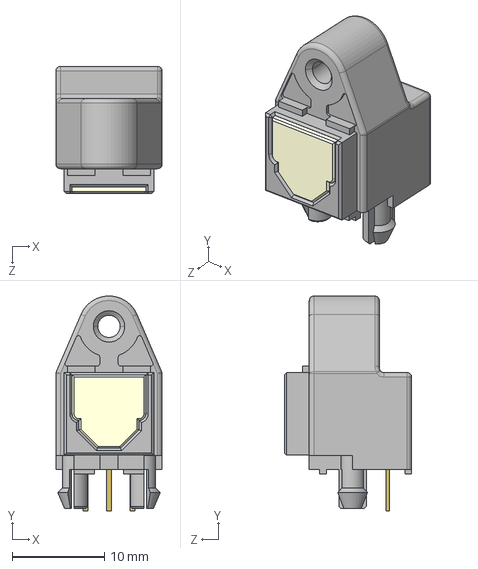
[picture p100: CAD file, 2025-03-24]
3d_models/TOSLINK_3D_MODEL_PLT133_T9.step
11.5 x 23.3 x 13.8 mm
