t-dsp/t-dsp_desktop_pro/3d_models/Same_Sky_SJ3-35083D-TR.step

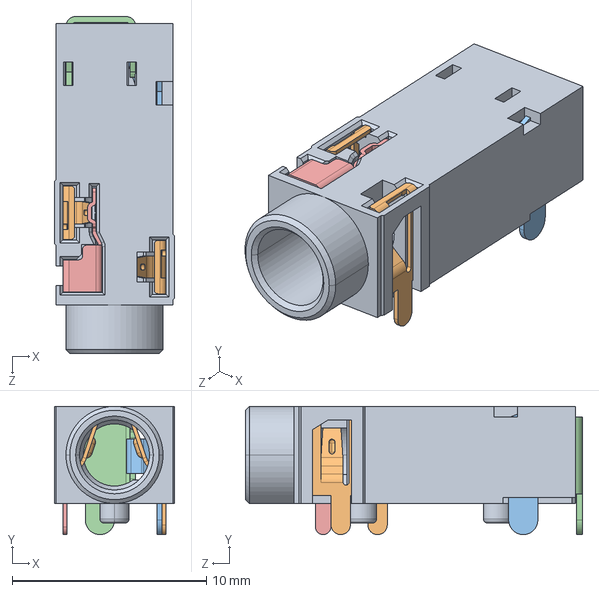
[picture p101: CAD file, 2025-03-24]
3d_models/Same_Sky_SJ3-35083D-TR.step
6.20 x 6.60 x 17.3 mm
