t-dsp/t-dsp_desktop_pro/3d_models/2120--3DModel-STEP-630548.STEP

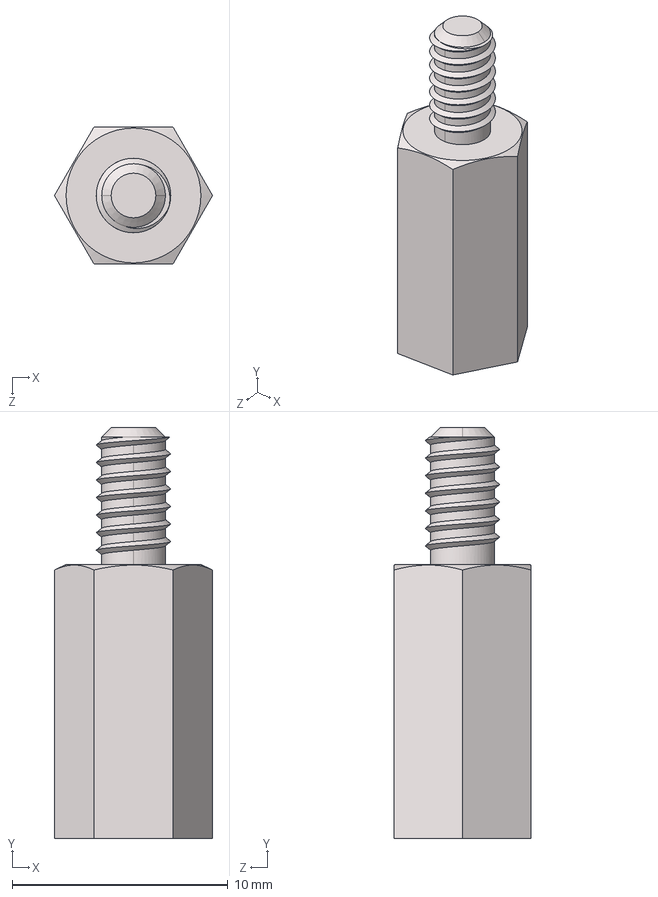
[picture p102: CAD file, 2025-03-24]
3d_models/2120--3DModel-STEP-630548.STEP
7.33 x 19.1 x 6.35 mm
