t-dsp/t-dsp_desktop_pro/3d_models/3.5MM_STEREO_35RAPC4BHN2.STEP

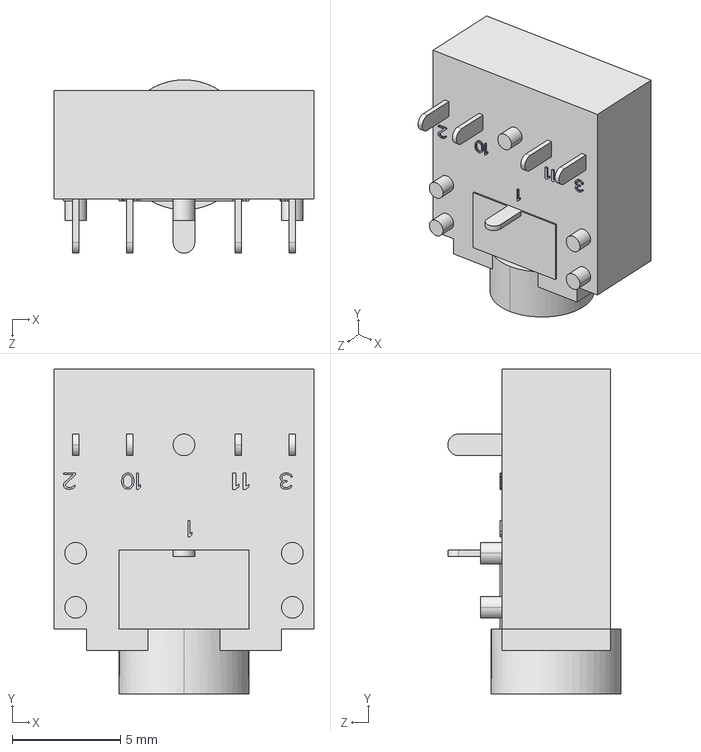
[picture p103: CAD file, 2025-03-24]
3d_models/3.5MM_STEREO_35RAPC4BHN2.STEP
12.0 x 15.0 x 8.00 mm
