t-dsp/t-dsp_desktop_pro/3d_models/ESP32-WROOM-32E_No-Cover.STEP

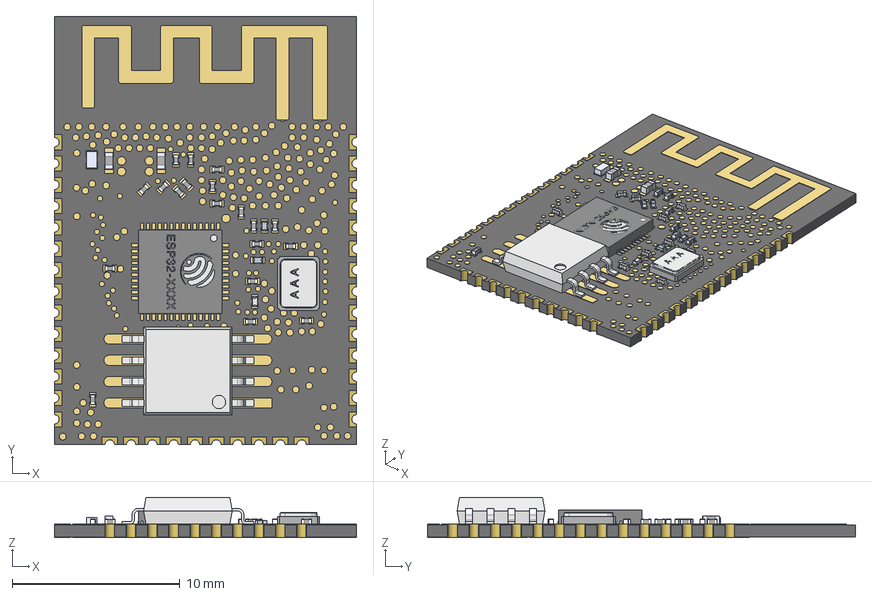
[picture p104: CAD file, 2025-03-24]
3d_models/ESP32-WROOM-32E_No-Cover.STEP
18.0 x 25.5 x 2.40 mm
ESP32_5x5_20210301.STEP^ESP32_5x5_20210301.STEP_Submodel-SLP48_5X5_ part_DesignRootModel_PCB_ESP32-WROOM-32E_V1(2)_PCB_ESP32-WROOM-32E_V1
trace_1^Submodel-ANT_L_TYPEA_1501846164_part_DesignRootModel_PCB_ ESP32-WROOM-32E_V1(2)_PCB_ESP32-WROOM-32E_V1
DFN1006.STEP^DFN1006.STEP_Submodel-SOD882_part_DesignRootModel_PCB_ ESP32-WROOM-32E_V1(2)_PCB_ESP32-WROOM-32E_V1
R0201_20210301.STEP^R0201_20210301.STEP_Submodel-R0201_part_ DesignRootModel_PCB_ESP32-WROOM-32E_V1(2)_PCB_ESP32-WROOM-32E_V1
R0201_20210301.STEP^R0201_20210301.STEP_Submodel-R0201_part_ DesignRootModel_PCB_ESP32-WROOM-32E_V1(2)_PCB_ESP32-WROOM-32E_V002
R0201_20210301.STEP^R0201_20210301.STEP_Submodel-R0201_part_ DesignRootModel_PCB_ESP32-WROOM-32E_V1(2)_PCB_ESP32-WROOM-32E_V003
L0201_20210301.STEP^L0201_20210301.STEP_Submodel-L0201_part_ DesignRootModel_PCB_ESP32-WROOM-32E_V1(2)_PCB_ESP32-WROOM-32E_V002 x 2
C0201_20210301.STEP^C0201_20210301.STEP_Submodel-C0201_part_ DesignRootModel_PCB_ESP32-WROOM-32E_V1(2)_PCB_ESP32-WROOM-32E_V017 x 17
SOIC8_208_20210301.STEP^SOIC8_208_20210301.STEP_Submodel-SOIC08-WN_ part_DesignRootModel_PCB_ESP32-WROOM-32E_V1(2)_PCB_ESP32-WROOM-32E_V1
XTAL3225_20210301.STEP^XTAL3225_20210301.STEP_Submodel-3225_part_ DesignRootModel_PCB_ESP32-WROOM-32E_V1(2)_PCB_ESP32-WROOM-32E_V1
C0402_20210301.STEP^C0402_20210301.STEP_Submodel-0402A_part_ DesignRootModel_PCB_ESP32-WROOM-32E_V1(2)_PCB_ESP32-WROOM-32E_V002 x 2
uid__1-311^DesignRootModel_PCB_ESP32-WROOM-32E_V1(2)_PCB_ ESP32-WROOM-32E_V1
uid__1-312^DesignRootModel_PCB_ESP32-WROOM-32E_V1(2)_PCB_ ESP32-WROOM-32E_V1
uid__1-313^DesignRootModel_PCB_ESP32-WROOM-32E_V1(2)_PCB_ ESP32-WROOM-32E_V1
uid__1-314^DesignRootModel_PCB_ESP32-WROOM-32E_V1(2)_PCB_ ESP32-WROOM-32E_V1
uid__1-315^DesignRootModel_PCB_ESP32-WROOM-32E_V1(2)_PCB_ ESP32-WROOM-32E_V1
uid__1-316^DesignRootModel_PCB_ESP32-WROOM-32E_V1(2)_PCB_ ESP32-WROOM-32E_V1
uid__1-317^DesignRootModel_PCB_ESP32-WROOM-32E_V1(2)_PCB_ ESP32-WROOM-32E_V1
uid__1-318^DesignRootModel_PCB_ESP32-WROOM-32E_V1(2)_PCB_ ESP32-WROOM-32E_V1
uid__1-319^DesignRootModel_PCB_ESP32-WROOM-32E_V1(2)_PCB_ ESP32-WROOM-32E_V1
uid__1-320^DesignRootModel_PCB_ESP32-WROOM-32E_V1(2)_PCB_ ESP32-WROOM-32E_V1
uid__1-321^DesignRootModel_PCB_ESP32-WROOM-32E_V1(2)_PCB_ ESP32-WROOM-32E_V1
uid__1-322^DesignRootModel_PCB_ESP32-WROOM-32E_V1(2)_PCB_ ESP32-WROOM-32E_V1
uid__1-323^DesignRootModel_PCB_ESP32-WROOM-32E_V1(2)_PCB_ ESP32-WROOM-32E_V1
uid__1-324^DesignRootModel_PCB_ESP32-WROOM-32E_V1(2)_PCB_ ESP32-WROOM-32E_V1
uid__1-325^DesignRootModel_PCB_ESP32-WROOM-32E_V1(2)_PCB_ ESP32-WROOM-32E_V1
uid__1-326^DesignRootModel_PCB_ESP32-WROOM-32E_V1(2)_PCB_ ESP32-WROOM-32E_V1
uid__1-327^DesignRootModel_PCB_ESP32-WROOM-32E_V1(2)_PCB_ ESP32-WROOM-32E_V1
uid__1-328^DesignRootModel_PCB_ESP32-WROOM-32E_V1(2)_PCB_ ESP32-WROOM-32E_V1
uid__1-329^DesignRootModel_PCB_ESP32-WROOM-32E_V1(2)_PCB_ ESP32-WROOM-32E_V1
uid__1-330^DesignRootModel_PCB_ESP32-WROOM-32E_V1(2)_PCB_ ESP32-WROOM-32E_V1
uid__1-331^DesignRootModel_PCB_ESP32-WROOM-32E_V1(2)_PCB_ ESP32-WROOM-32E_V1
uid__1-332^DesignRootModel_PCB_ESP32-WROOM-32E_V1(2)_PCB_ ESP32-WROOM-32E_V1
uid__1-333^DesignRootModel_PCB_ESP32-WROOM-32E_V1(2)_PCB_ ESP32-WROOM-32E_V1
uid__1-334^DesignRootModel_PCB_ESP32-WROOM-32E_V1(2)_PCB_ ESP32-WROOM-32E_V1
uid__1-335^DesignRootModel_PCB_ESP32-WROOM-32E_V1(2)_PCB_ ESP32-WROOM-32E_V1
uid__1-336^DesignRootModel_PCB_ESP32-WROOM-32E_V1(2)_PCB_ ESP32-WROOM-32E_V1
uid__1-337^DesignRootModel_PCB_ESP32-WROOM-32E_V1(2)_PCB_ ESP32-WROOM-32E_V1
uid__1-338^DesignRootModel_PCB_ESP32-WROOM-32E_V1(2)_PCB_ ESP32-WROOM-32E_V1
uid__1-339^DesignRootModel_PCB_ESP32-WROOM-32E_V1(2)_PCB_ ESP32-WROOM-32E_V1
uid__1-340^DesignRootModel_PCB_ESP32-WROOM-32E_V1(2)_PCB_ ESP32-WROOM-32E_V1
uid__1-341^DesignRootModel_PCB_ESP32-WROOM-32E_V1(2)_PCB_ ESP32-WROOM-32E_V1
uid__1-342^DesignRootModel_PCB_ESP32-WROOM-32E_V1(2)_PCB_ ESP32-WROOM-32E_V1
uid__1-343^DesignRootModel_PCB_ESP32-WROOM-32E_V1(2)_PCB_ ESP32-WROOM-32E_V1
uid__1-344^DesignRootModel_PCB_ESP32-WROOM-32E_V1(2)_PCB_ ESP32-WROOM-32E_V1
uid__1-345^DesignRootModel_PCB_ESP32-WROOM-32E_V1(2)_PCB_ ESP32-WROOM-32E_V1
uid__1-346^DesignRootModel_PCB_ESP32-WROOM-32E_V1(2)_PCB_ ESP32-WROOM-32E_V1
uid__1-347^DesignRootModel_PCB_ESP32-WROOM-32E_V1(2)_PCB_ ESP32-WROOM-32E_V1
uid__1-348^DesignRootModel_PCB_ESP32-WROOM-32E_V1(2)_PCB_ ESP32-WROOM-32E_V1
uid__1-349^DesignRootModel_PCB_ESP32-WROOM-32E_V1(2)_PCB_ ESP32-WROOM-32E_V1
uid__1-350^DesignRootModel_PCB_ESP32-WROOM-32E_V1(2)_PCB_ ESP32-WROOM-32E_V1
uid__1-351^DesignRootModel_PCB_ESP32-WROOM-32E_V1(2)_PCB_ ESP32-WROOM-32E_V1
uid__1-352^DesignRootModel_PCB_ESP32-WROOM-32E_V1(2)_PCB_ ESP32-WROOM-32E_V1
uid__1-353^DesignRootModel_PCB_ESP32-WROOM-32E_V1(2)_PCB_ ESP32-WROOM-32E_V1
uid__1-354^DesignRootModel_PCB_ESP32-WROOM-32E_V1(2)_PCB_ ESP32-WROOM-32E_V1
uid__1-355^DesignRootModel_PCB_ESP32-WROOM-32E_V1(2)_PCB_ ESP32-WROOM-32E_V1
uid__1-356^DesignRootModel_PCB_ESP32-WROOM-32E_V1(2)_PCB_ ESP32-WROOM-32E_V1
uid__1-357^DesignRootModel_PCB_ESP32-WROOM-32E_V1(2)_PCB_ ESP32-WROOM-32E_V1
uid__1-359^DesignRootModel_PCB_ESP32-WROOM-32E_V1(2)_PCB_ ESP32-WROOM-32E_V1
uid__1-360^DesignRootModel_PCB_ESP32-WROOM-32E_V1(2)_PCB_ ESP32-WROOM-32E_V1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
