t-dsp/t-dsp_desktop_pro/3d_models/ESP32-DEVKITC-32D.step

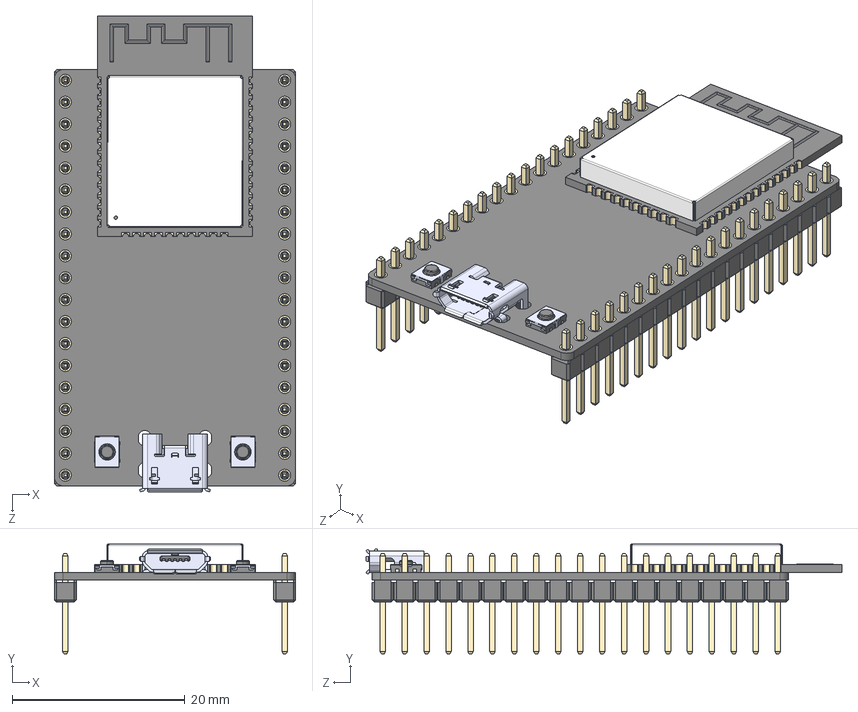
[picture p105: CAD file, 2025-03-24]
3d_models/ESP32-DEVKITC-32D.step
27.9 x 12.7 x 55.1 mm
board
header x 2
ESP32-WROOM-32D
micro usb
button x 2
