t-dsp/t-dsp_desktop_pro/3d_models/SPDIF_pjran1x1_Series.STEP

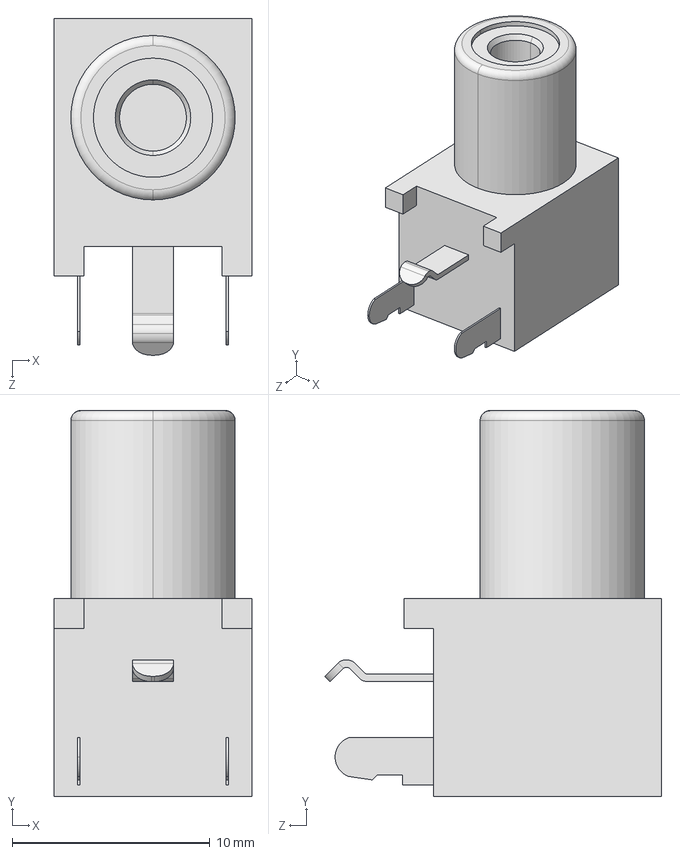
[picture p106: CAD file, 2025-03-24]
3d_models/SPDIF_pjran1x1_Series.STEP
10.00 x 19.5 x 17.0 mm
