t-dsp/t-dsp_desktop_pro/3d_models/USB-B1HS - USB-B1H Interconnect USB Type B.stp

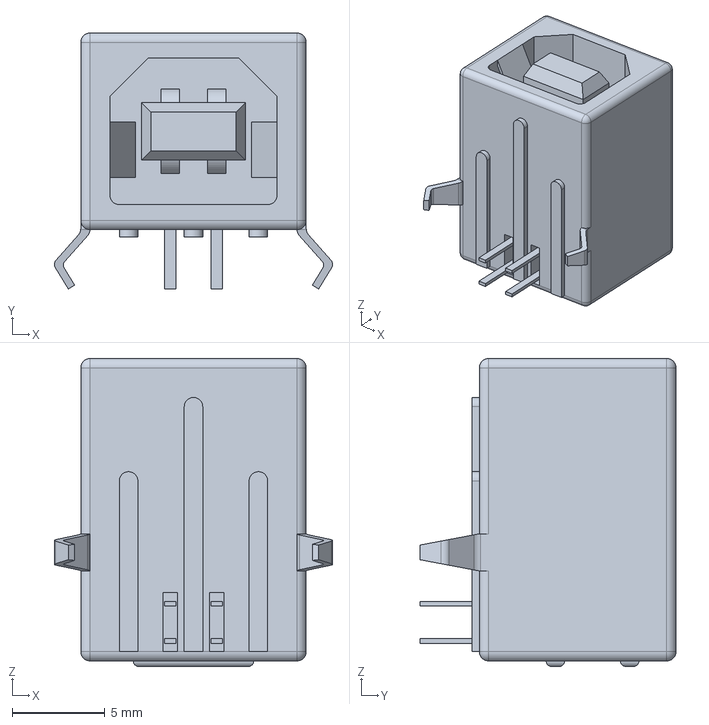
[picture p107: CAD file, 2025-03-24]
3d_models/USB-B1HS - USB-B1H Interconnect USB Type B.stp
15.0 x 13.8 x 16.6 mm
