t-dsp/t-dsp_desktop_pro/3d_models/USB_A_c-292303-4-f-3d.stp

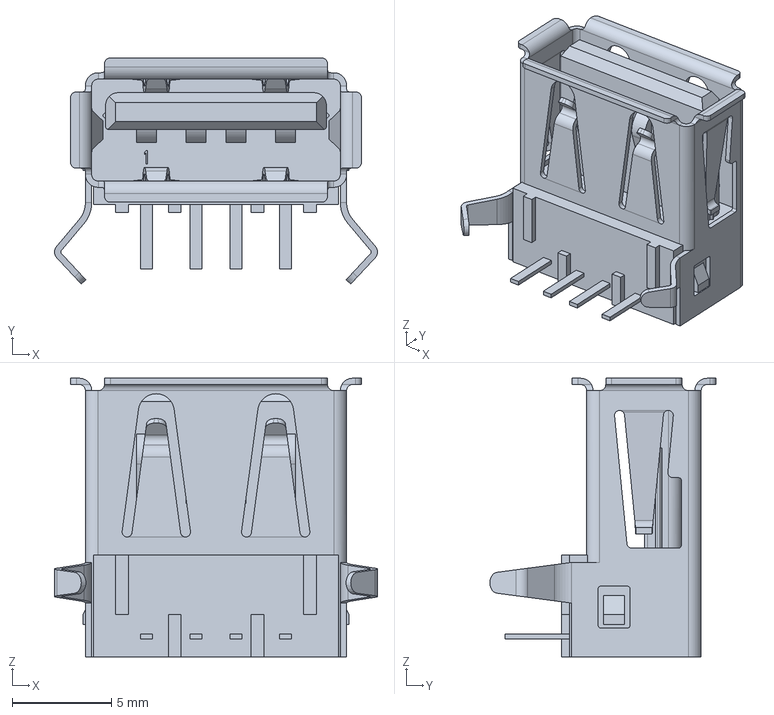
[picture p108: CAD file, 2025-03-24]
3d_models/USB_A_c-292303-4-f-3d.stp
16.2 x 11.4 x 14.0 mm
