t-dsp/t-dsp_desktop_pro/3d_models/ncj6fav-1.stp

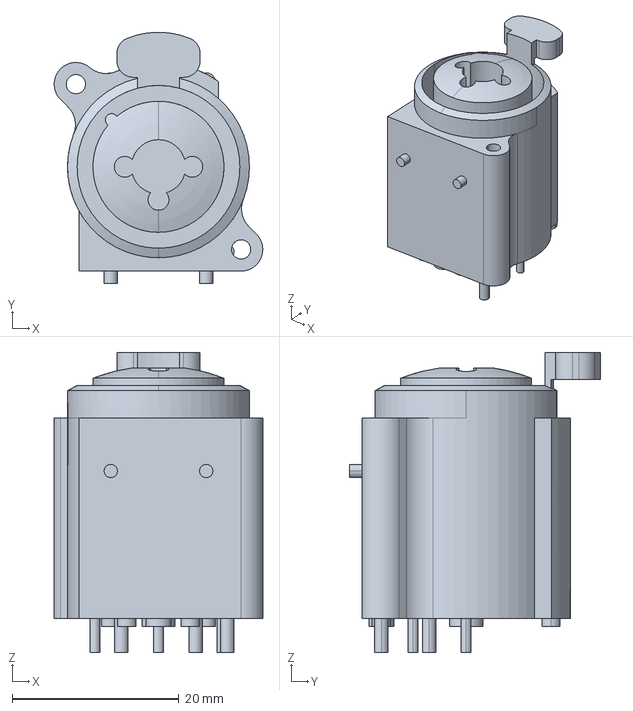
[picture p109: CAD file, 2025-03-24]
3d_models/ncj6fav-1.stp
25.0 x 30.1 x 36.0 mm
