t-dsp/t-dsp_desktop_pro/3d_models/SOIC-14_3.9x8.7mm_P1.27mm.step

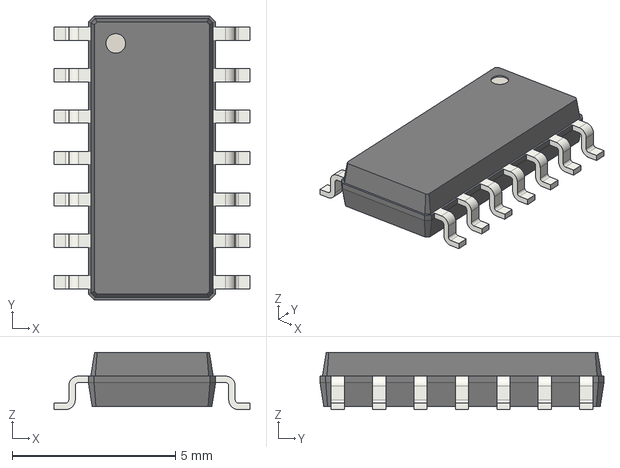
[picture p110: CAD file, 2025-03-24]
3d_models/SOIC-14_3.9x8.7mm_P1.27mm.step
6.00 x 8.70 x 1.75 mm
