t-dsp/t-dsp_desktop_pro/3d_models/pjras2x2s_Series - Copy.STEP

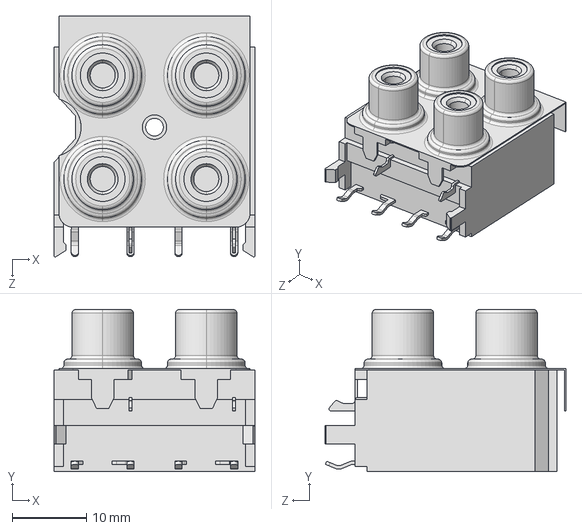
[picture p111: CAD file, 2025-03-24]
3d_models/pjras2x2s_Series - Copy.STEP
27.2 x 21.9 x 32.5 mm
