t-dsp/t-dsp_desktop_pro/3d_models/SOIC-14W_7.5x9.0mm_P1.27mm.step

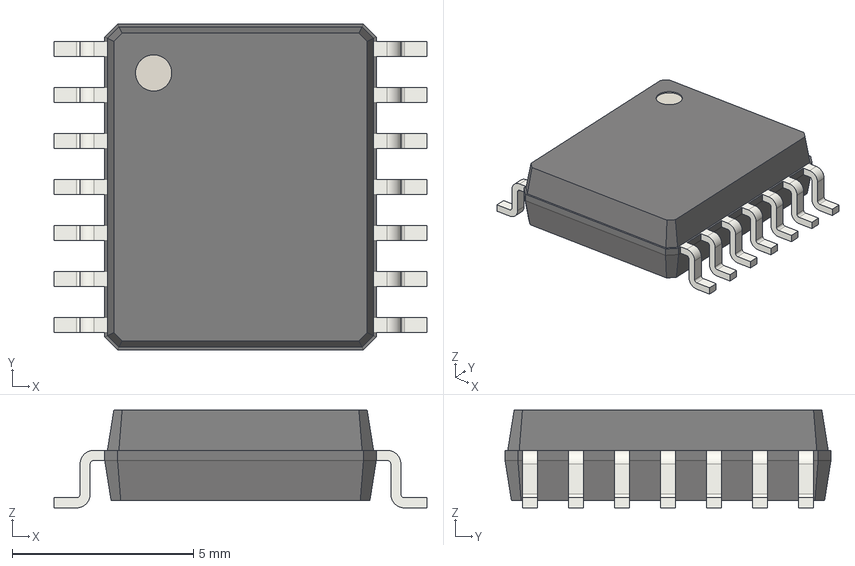
[picture p112: CAD file, 2025-03-24]
3d_models/SOIC-14W_7.5x9.0mm_P1.27mm.step
10.3 x 9.00 x 2.70 mm
