t-dsp/t-dsp_desktop_pro/3d_models/ESP32-WROOM-32UE.STEP

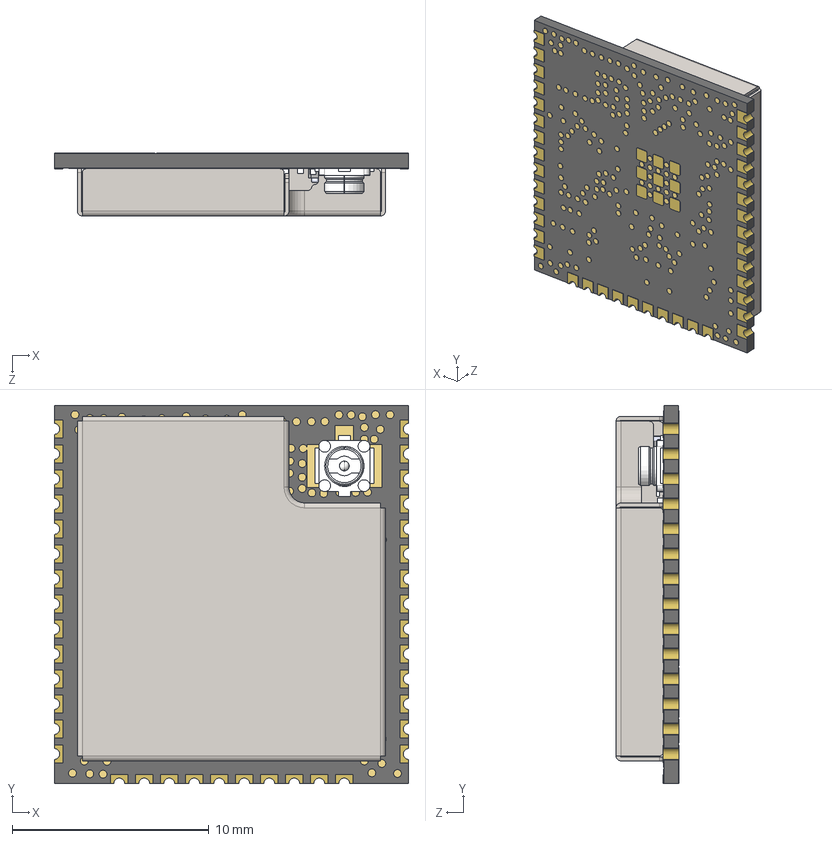
[picture p113: CAD file, 2025-03-24]
3d_models/ESP32-WROOM-32UE.STEP
18.0 x 19.2 x 3.20 mm
ESP32_5x5_20210301.STEP^ESP32_5x5_20210301.STEP_Submodel-QFN48EB_0P35_5_part_DesignRootModel_PCB_ESP32-WROOM-32UE_V1(2)_PCB_ESP32-WROOM-32UE_V1
20279-001E-01C RECEPTACLE R9 STEP ALL.STEP^20279-001E-01C RECEPTACLE R9 STEP ALL.STEP_Submodel-ECT818000368_part_DesignRootModel_PCB_ESP32-WROOM-32UE_V1(2)_PCB_
DFN1006.STEP^DFN1006.STEP_Submodel-SOD882_part_DesignRootModel_PCB_ESP32-WROOM-32UE_V1(2)_PCB_ESP32-WROOM-32UE_V1
XTAL3225_20210301.STEP^XTAL3225_20210301.STEP_Submodel-XTAL3225_part_DesignRootModel_PCB_ESP32-WROOM-32UE_V1(2)_PCB_ESP32-WROOM-32UE_V1
C0402_20210301.STEP^C0402_20210301.STEP_Submodel-C0402_part_DesignRootModel_PCB_ESP32-WROOM-32UE_V1(2)_PCB_ESP32-WROOM-32UE_V1
SOIC8_208_20210301.STEP^SOIC8_208_20210301.STEP_Submodel-SOP8_1P27_6P6_part_DesignRootModel_PCB_ESP32-WROOM-32UE_V1(2)_PCB_ESP32-WROOM-32UE_V1
L0201_20210301.STEP^L0201_20210301.STEP_Submodel-L0201_part_DesignRootModel_PCB_ESP32-WROOM-32UE_V1(2)_PCB_ESP32-WROOM-32UE_V1 x 2
R0201_20210301.STEP^R0201_20210301.STEP_Submodel-R0201_part_DesignRootModel_PCB_ESP32-WROOM-32UE_V1(2)_PCB_ESP32-WROOM-32UE_V1 x 3
C0201_20210301.STEP^C0201_20210301.STEP_Submodel-C0201_part_DesignRootModel_PCB_ESP32-WROOM-32UE_V1(2)_PCB_ESP32-WROOM-32UE_V1 x 15
uid__4-13^DesignRootModel_PCB_ESP32-WROOM-32UE_V1(2)_PCB_ESP32-WROOM-32UE_V1
uid__4-14^DesignRootModel_PCB_ESP32-WROOM-32UE_V1(2)_PCB_ESP32-WROOM-32UE_V1
uid__4-15^DesignRootModel_PCB_ESP32-WROOM-32UE_V1(2)_PCB_ESP32-WROOM-32UE_V1
uid__4-16^DesignRootModel_PCB_ESP32-WROOM-32UE_V1(2)_PCB_ESP32-WROOM-32UE_V1
uid__4-17^DesignRootModel_PCB_ESP32-WROOM-32UE_V1(2)_PCB_ESP32-WROOM-32UE_V1
uid__4-18^DesignRootModel_PCB_ESP32-WROOM-32UE_V1(2)_PCB_ESP32-WROOM-32UE_V1
uid__4-19^DesignRootModel_PCB_ESP32-WROOM-32UE_V1(2)_PCB_ESP32-WROOM-32UE_V1
uid__4-20^DesignRootModel_PCB_ESP32-WROOM-32UE_V1(2)_PCB_ESP32-WROOM-32UE_V1
uid__4-21^DesignRootModel_PCB_ESP32-WROOM-32UE_V1(2)_PCB_ESP32-WROOM-32UE_V1
uid__4-22^DesignRootModel_PCB_ESP32-WROOM-32UE_V1(2)_PCB_ESP32-WROOM-32UE_V1
uid__4-23^DesignRootModel_PCB_ESP32-WROOM-32UE_V1(2)_PCB_ESP32-WROOM-32UE_V1
uid__4-24^DesignRootModel_PCB_ESP32-WROOM-32UE_V1(2)_PCB_ESP32-WROOM-32UE_V1
uid__4-25^DesignRootModel_PCB_ESP32-WROOM-32UE_V1(2)_PCB_ESP32-WROOM-32UE_V1
uid__4-26^DesignRootModel_PCB_ESP32-WROOM-32UE_V1(2)_PCB_ESP32-WROOM-32UE_V1
uid__4-27^DesignRootModel_PCB_ESP32-WROOM-32UE_V1(2)_PCB_ESP32-WROOM-32UE_V1
uid__4-28^DesignRootModel_PCB_ESP32-WROOM-32UE_V1(2)_PCB_ESP32-WROOM-32UE_V1
uid__4-29^DesignRootModel_PCB_ESP32-WROOM-32UE_V1(2)_PCB_ESP32-WROOM-32UE_V1
uid__4-30^DesignRootModel_PCB_ESP32-WROOM-32UE_V1(2)_PCB_ESP32-WROOM-32UE_V1
uid__4-31^DesignRootModel_PCB_ESP32-WROOM-32UE_V1(2)_PCB_ESP32-WROOM-32UE_V1
uid__4-32^DesignRootModel_PCB_ESP32-WROOM-32UE_V1(2)_PCB_ESP32-WROOM-32UE_V1
uid__4-33^DesignRootModel_PCB_ESP32-WROOM-32UE_V1(2)_PCB_ESP32-WROOM-32UE_V1
uid__4-34^DesignRootModel_PCB_ESP32-WROOM-32UE_V1(2)_PCB_ESP32-WROOM-32UE_V1
uid__4-35^DesignRootModel_PCB_ESP32-WROOM-32UE_V1(2)_PCB_ESP32-WROOM-32UE_V1
uid__4-36^DesignRootModel_PCB_ESP32-WROOM-32UE_V1(2)_PCB_ESP32-WROOM-32UE_V1
uid__4-37^DesignRootModel_PCB_ESP32-WROOM-32UE_V1(2)_PCB_ESP32-WROOM-32UE_V1
uid__4-38^DesignRootModel_PCB_ESP32-WROOM-32UE_V1(2)_PCB_ESP32-WROOM-32UE_V1
uid__4-39^DesignRootModel_PCB_ESP32-WROOM-32UE_V1(2)_PCB_ESP32-WROOM-32UE_V1
uid__4-40^DesignRootModel_PCB_ESP32-WROOM-32UE_V1(2)_PCB_ESP32-WROOM-32UE_V1
uid__4-41^DesignRootModel_PCB_ESP32-WROOM-32UE_V1(2)_PCB_ESP32-WROOM-32UE_V1
uid__4-42^DesignRootModel_PCB_ESP32-WROOM-32UE_V1(2)_PCB_ESP32-WROOM-32UE_V1
uid__4-43^DesignRootModel_PCB_ESP32-WROOM-32UE_V1(2)_PCB_ESP32-WROOM-32UE_V1
uid__4-45^DesignRootModel_PCB_ESP32-WROOM-32UE_V1(2)_PCB_ESP32-WROOM-32UE_V1
uid__4-46^DesignRootModel_PCB_ESP32-WROOM-32UE_V1(2)_PCB_ESP32-WROOM-32UE_V1
uid__4-47^DesignRootModel_PCB_ESP32-WROOM-32UE_V1(2)_PCB_ESP32-WROOM-32UE_V1
uid__4-48^DesignRootModel_PCB_ESP32-WROOM-32UE_V1(2)_PCB_ESP32-WROOM-32UE_V1
uid__4-49^DesignRootModel_PCB_ESP32-WROOM-32UE_V1(2)_PCB_ESP32-WROOM-32UE_V1
uid__4-50^DesignRootModel_PCB_ESP32-WROOM-32UE_V1(2)_PCB_ESP32-WROOM-32UE_V1
uid__4-51^DesignRootModel_PCB_ESP32-WROOM-32UE_V1(2)_PCB_ESP32-WROOM-32UE_V1
uid__4-52^DesignRootModel_PCB_ESP32-WROOM-32UE_V1(2)_PCB_ESP32-WROOM-32UE_V1
uid__4-53^DesignRootModel_PCB_ESP32-WROOM-32UE_V1(2)_PCB_ESP32-WROOM-32UE_V1
uid__4-54^DesignRootModel_PCB_ESP32-WROOM-32UE_V1(2)_PCB_ESP32-WROOM-32UE_V1
uid__4-55^DesignRootModel_PCB_ESP32-WROOM-32UE_V1(2)_PCB_ESP32-WROOM-32UE_V1
uid__4-56^DesignRootModel_PCB_ESP32-WROOM-32UE_V1(2)_PCB_ESP32-WROOM-32UE_V1
uid__4-57^DesignRootModel_PCB_ESP32-WROOM-32UE_V1(2)_PCB_ESP32-WROOM-32UE_V1
uid__4-58^DesignRootModel_PCB_ESP32-WROOM-32UE_V1(2)_PCB_ESP32-WROOM-32UE_V1
uid__4-60^DesignRootModel_PCB_ESP32-WROOM-32UE_V1(2)_PCB_ESP32-WROOM-32UE_V1
uid__4-61^DesignRootModel_PCB_ESP32-WROOM-32UE_V1(2)_PCB_ESP32-WROOM-32UE_V1
uid__4-62^DesignRootModel_PCB_ESP32-WROOM-32UE_V1(2)_PCB_ESP32-WROOM-32UE_V1
uid__4-63^DesignRootModel_PCB_ESP32-WROOM-32UE_V1(2)_PCB_ESP32-WROOM-32UE_V1
uid__4-64^DesignRootModel_PCB_ESP32-WROOM-32UE_V1(2)_PCB_ESP32-WROOM-32UE_V1
uid__4-65^DesignRootModel_PCB_ESP32-WROOM-32UE_V1(2)_PCB_ESP32-WROOM-32UE_V1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
