t-dsp/t-dsp_desktop_pro/3d_models/ESP32 WROOMU.step

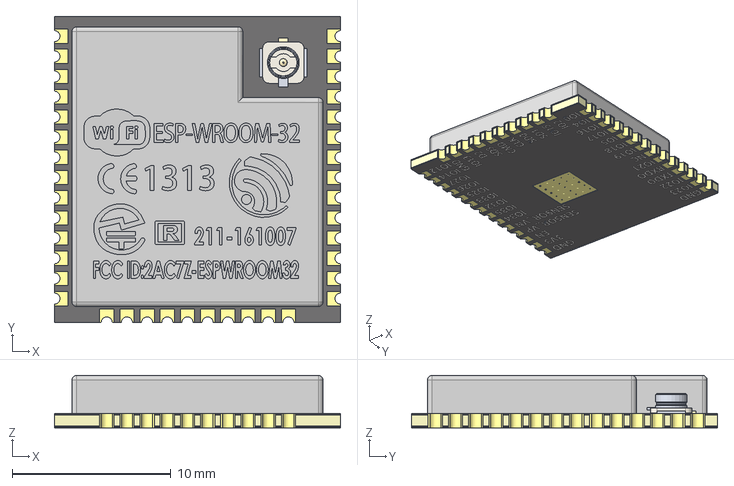
[picture p114: CAD file, 2025-03-24]
3d_models/ESP32 WROOMU.step
18.0 x 19.2 x 3.32 mm
