t-dsp/t-dsp_desktop_pro/3d_models/USB4085-GF-A.stp

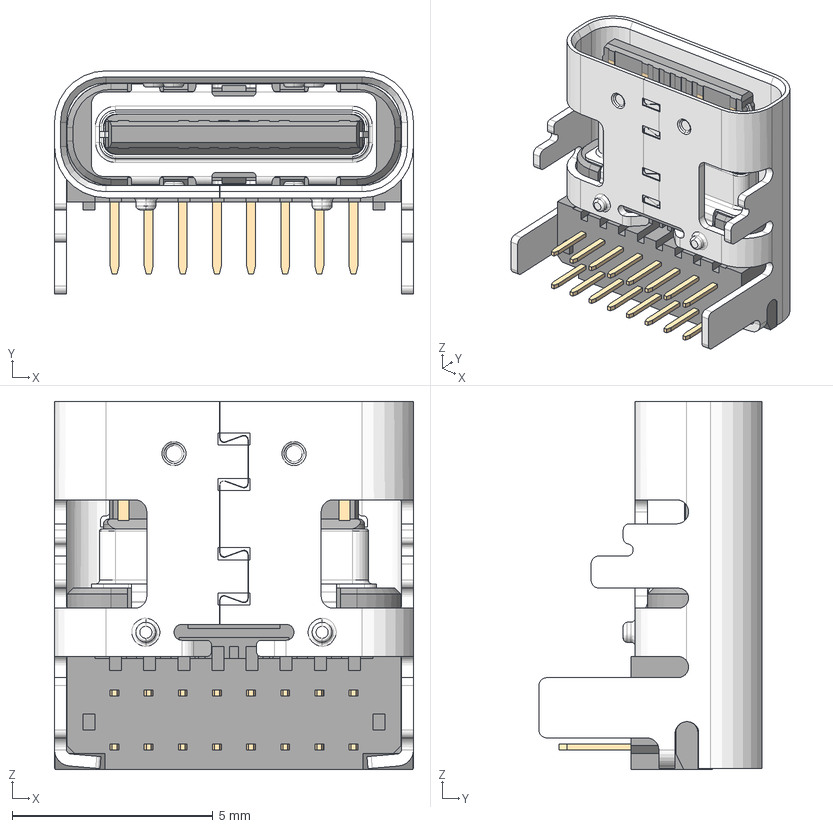
[picture p115: CAD file, 2025-03-24]
3d_models/USB4085-GF-A.stp
8.94 x 5.56 x 9.17 mm
USB4085-GF-A_PART3
USB4085-GF-A_PART2
USB4085-GF-A_PART1
