t-dsp/t-dsp_desktop_pro/3d_models/pjras1x2s_Series - Copy.STEP

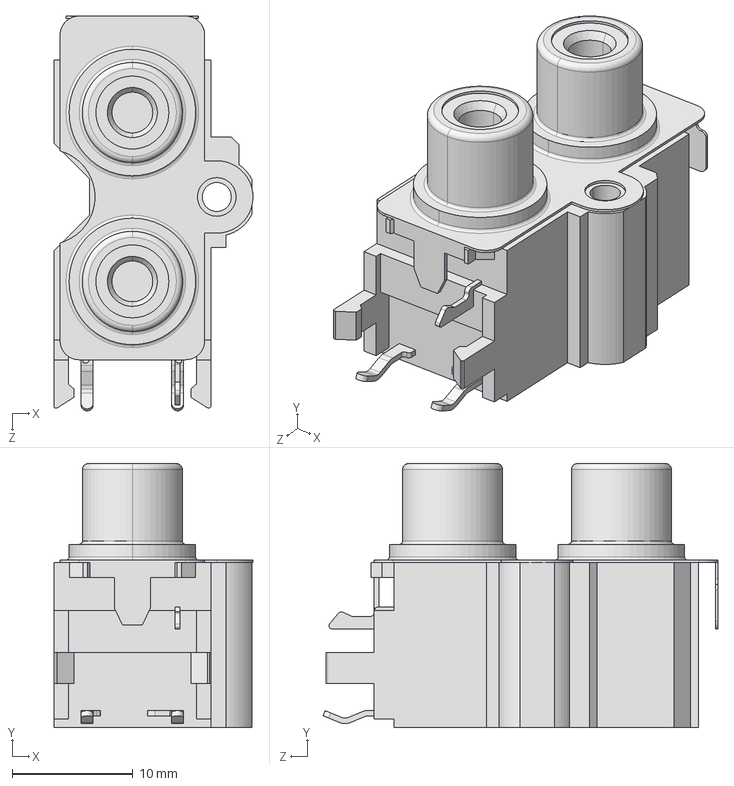
[picture p116: CAD file, 2025-03-24]
3d_models/pjras1x2s_Series - Copy.STEP
16.5 x 21.9 x 32.7 mm
