t-dsp/t-dsp_desktop_pro/3d_models/PEC12R-2220F-S0024.step

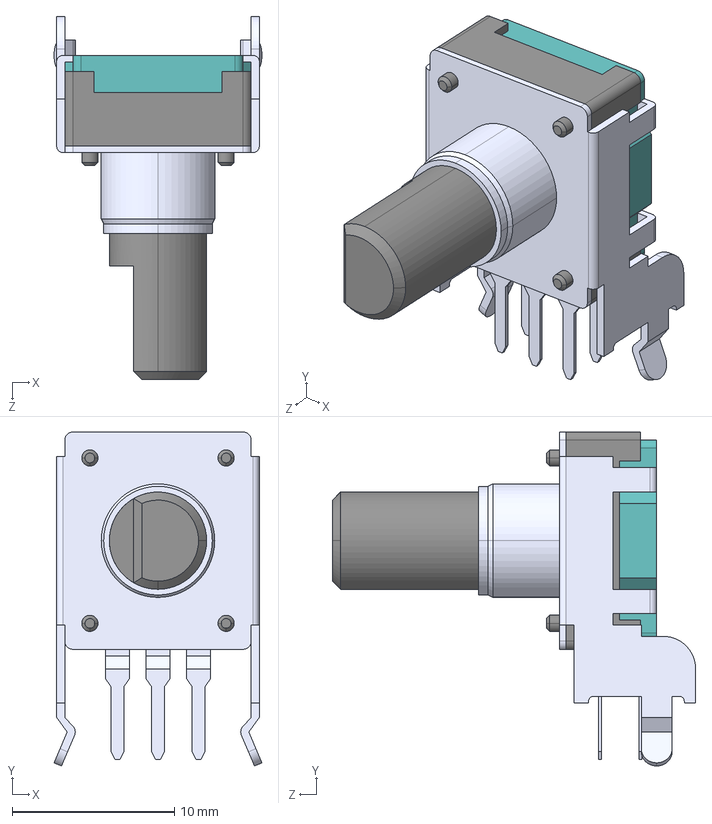
[picture p117: CAD file, 2025-03-24]
3d_models/PEC12R-2220F-S0024.step
12.8 x 20.6 x 22.4 mm
