t-dsp/t-dsp_desktop_pro/3d_models/DC_BARREL_PJ-202AH.step

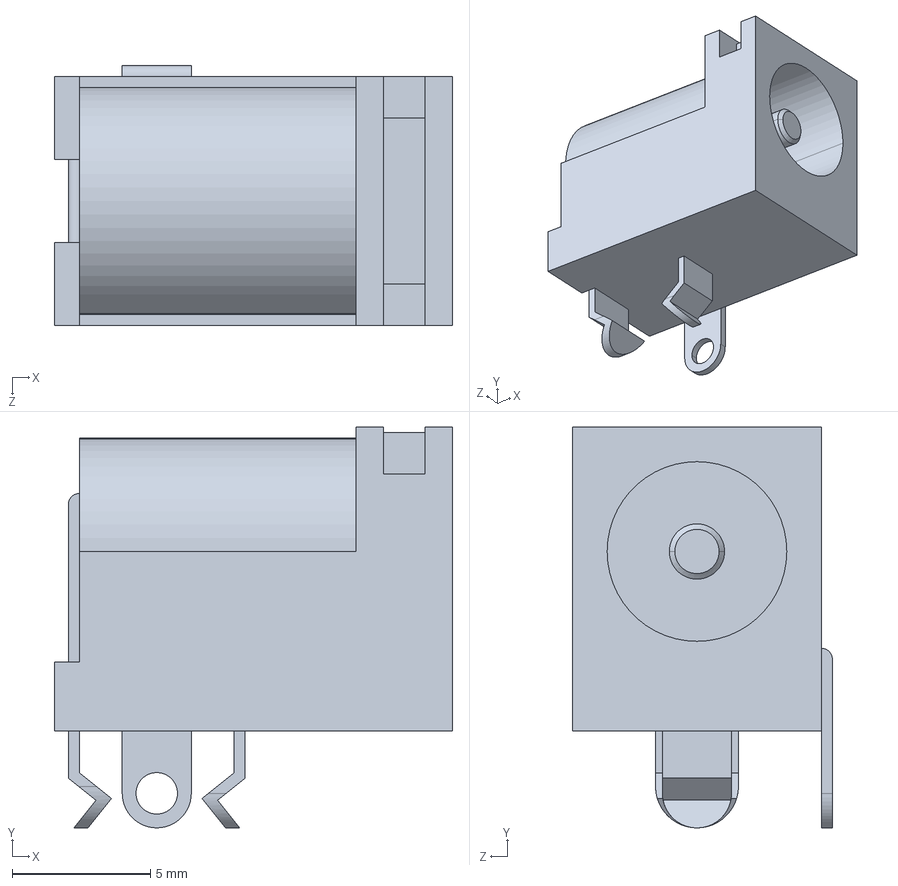
[picture p118: CAD file, 2025-03-24]
3d_models/DC_BARREL_PJ-202AH.step
14.4 x 14.5 x 9.40 mm
