t-dsp/t-dsp_desktop_pro/3d_models/J1B1211CCD.STEP

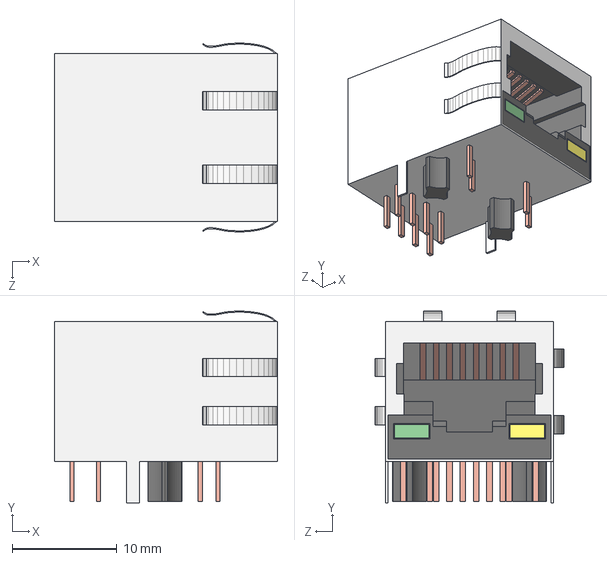
[picture p119: CAD file, 2025-03-24]
3d_models/J1B1211CCD.STEP
21.3 x 18.3 x 18.0 mm
