t-dsp/t-dsp_desktop_pro/3d_models/35RAPC3BH3.STEP

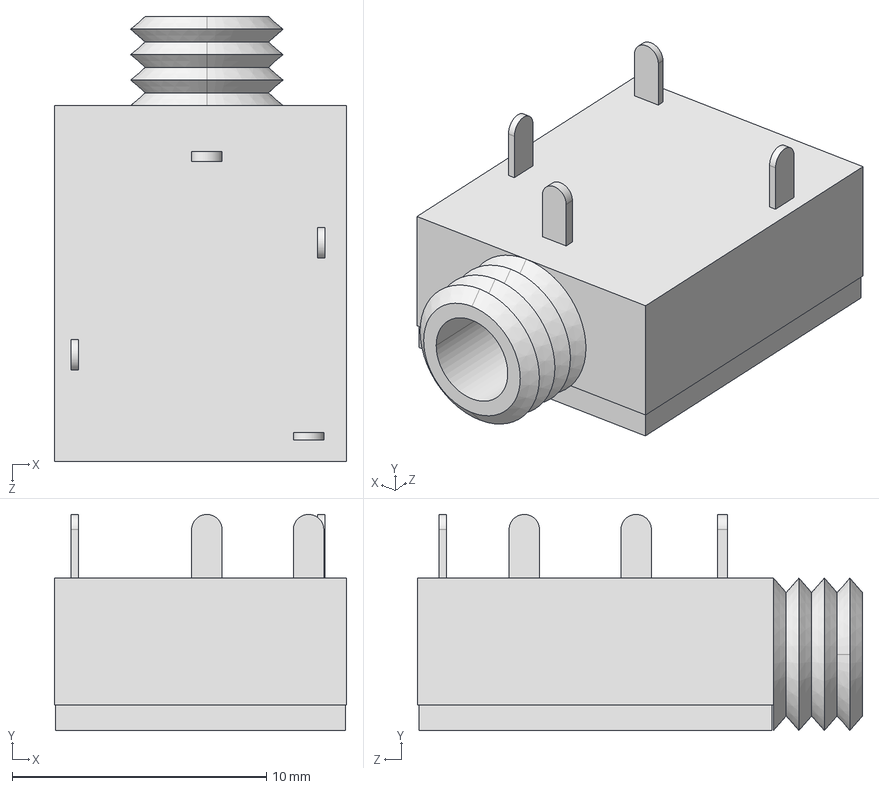
[picture p120: CAD file, 2025-03-24]
3d_models/35RAPC3BH3.STEP
11.5 x 8.50 x 17.5 mm
