t-dsp/t-dsp_desktop_pro/3d_models/JST - XH - Thru (V) - 2Pin - 2.54mm.stp

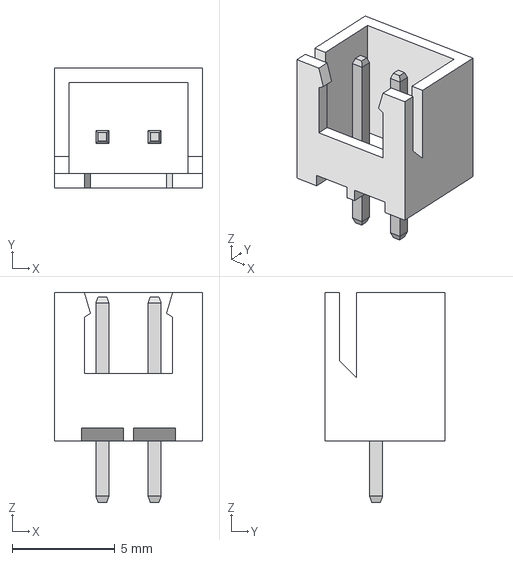
[picture p121: CAD file, 2025-03-24]
3d_models/JST - XH - Thru (V) - 2Pin - 2.54mm.stp
7.21 x 5.84 x 10.2 mm
