t-dsp/t-dsp_desktop_pro/3d_models/1808--3DModel-STEP-630548.STEP

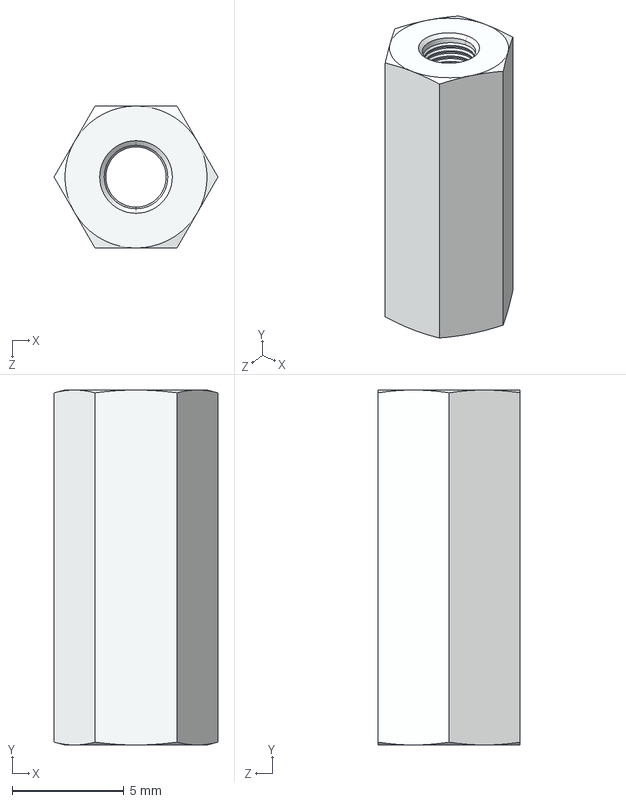
[picture p122: CAD file, 2025-03-24]
3d_models/1808--3DModel-STEP-630548.STEP
7.33 x 15.9 x 6.35 mm
