t-dsp/t-dsp_desktop_pro/3d_models/3-D NCJ6FAH.stp

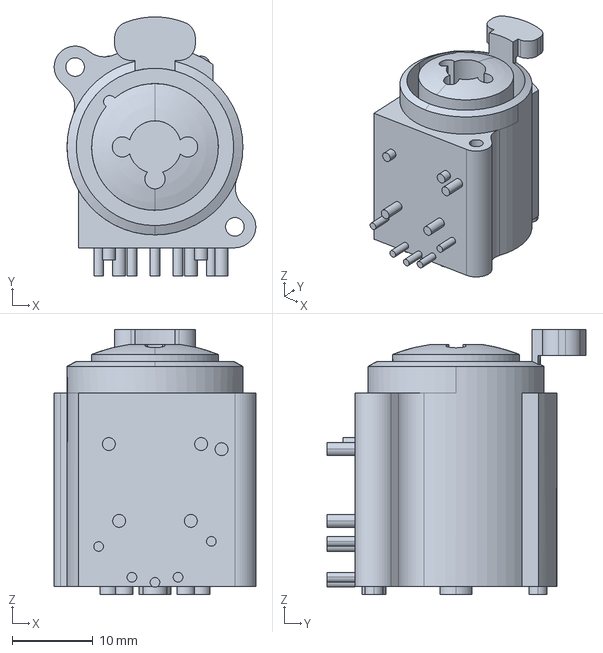
[picture p123: CAD file, 2025-03-24]
3d_models/3-D NCJ6FAH.stp
25.0 x 32.1 x 32.9 mm
