t-dsp/t-dsp_desktop_pro/3d_models/35RAPC7JS.STEP

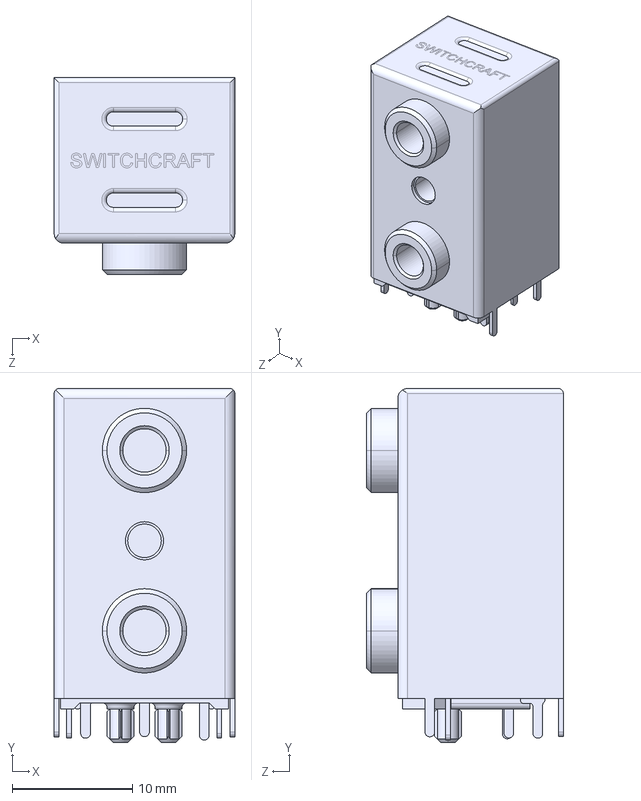
[picture p124: CAD file, 2025-03-24]
3d_models/35RAPC7JS.STEP
15.0 x 29.5 x 16.4 mm
