t-dsp/t-dsp_desktop_pro/3d_models/Same_Sky_SJ3-35044A.step

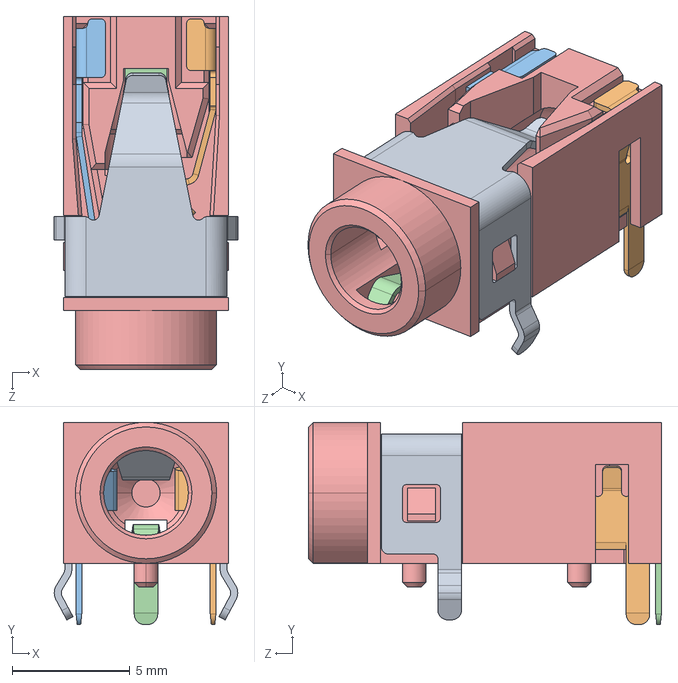
[picture p125: CAD file, 2025-03-24]
3d_models/Same_Sky_SJ3-35044A.step
7.80 x 8.60 x 15.0 mm
