t-dsp/t-dsp_desktop_pro/3d_models/SO-8_5.3x6.2mm_P1.27mm.step

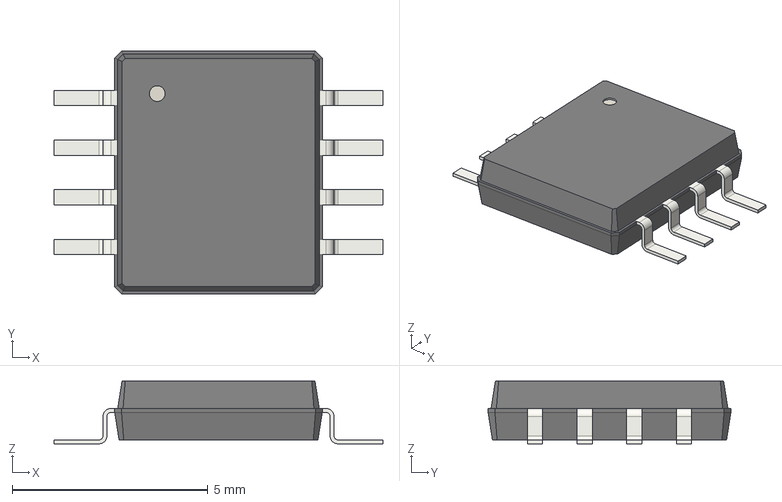
[picture p126: CAD file, 2025-03-24]
3d_models/SO-8_5.3x6.2mm_P1.27mm.step
8.40 x 6.20 x 1.60 mm
