t-dsp/t-dsp_desktop_pro/3d_models/3-d-nmj6hcd3.stp

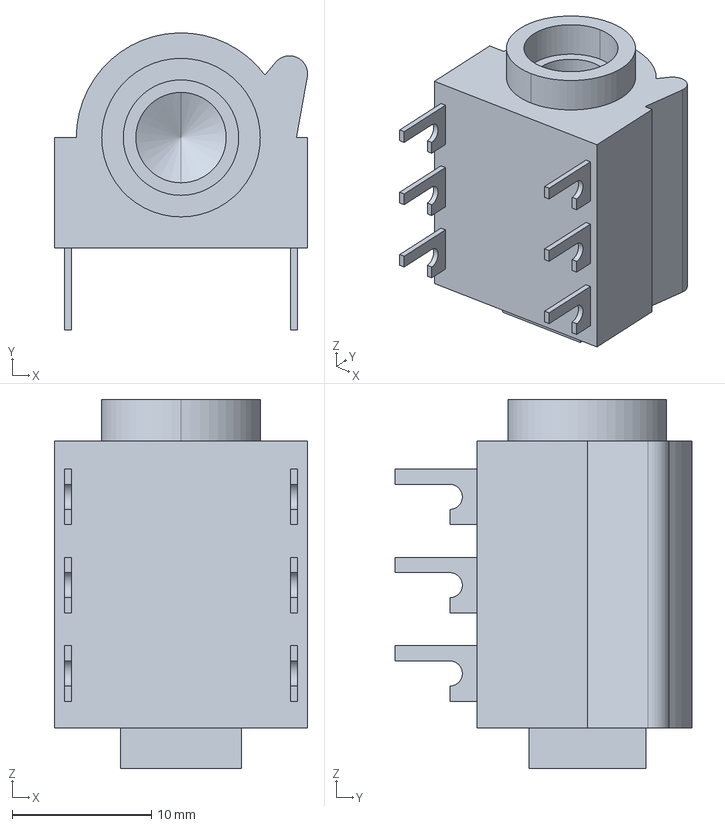
[picture p127: CAD file, 2025-03-24]
3d_models/3-d-nmj6hcd3.stp
18.2 x 21.4 x 26.5 mm
