t-dsp/t-dsp_desktop_pro/3d_models/4691.step

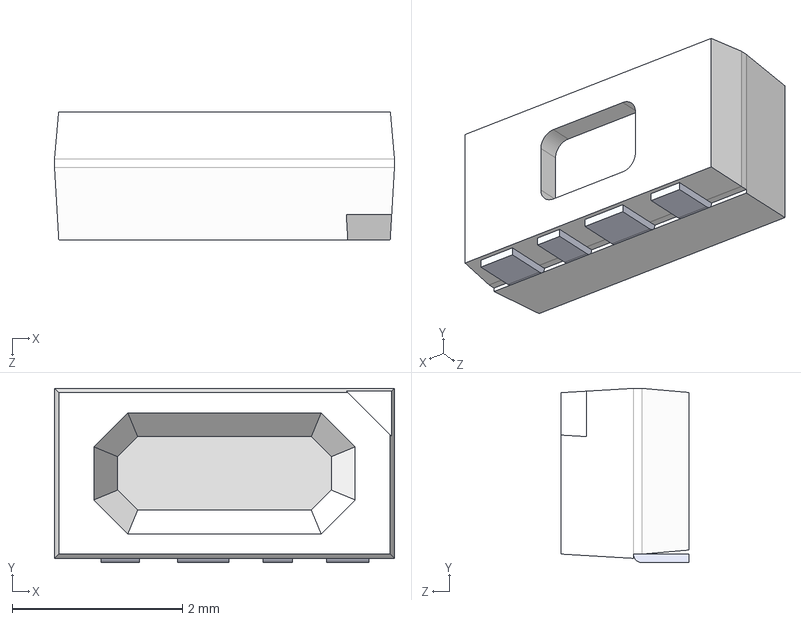
[picture p128: CAD file, 2025-03-24]
3d_models/4691.step
4.00 x 2.05 x 1.50 mm
