t-dsp/t-dsp_desktop_pro/3d_models/TE_1775485-1_BATTERY.step

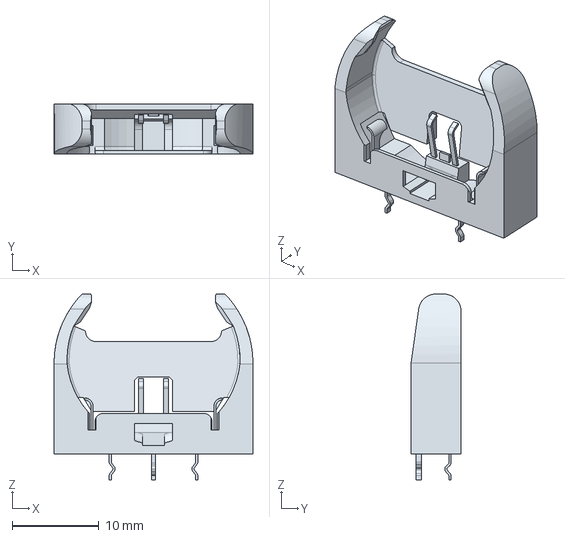
[picture p129: CAD file, 2025-03-24]
3d_models/TE_1775485-1_BATTERY.step
23.0 x 5.80 x 21.5 mm
